AxxAxx/AxxSolder/photos/C210-029_cross_section.jpg

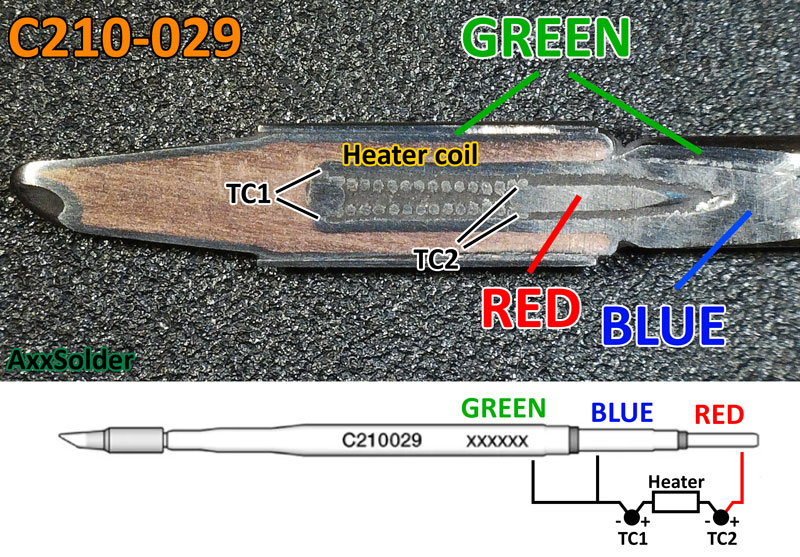
photos/C210-029_cross_section.jpg
