AxxAxx/AxxSolder/photos/C245-945_cross_section.jpg

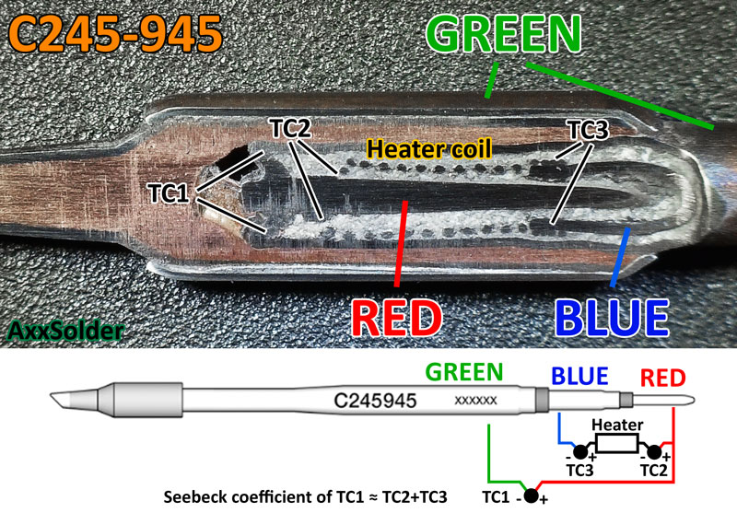
photos/C245-945_cross_section.jpg
