AxxAxx/AxxSolder/photos/cartridges_cross_sections.jpg

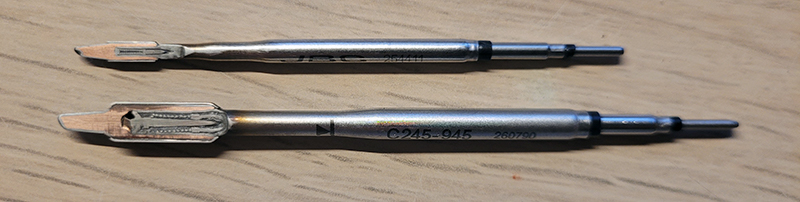
photos/cartridges_cross_sections.jpg
