AxxAxx/AxxSolder/photos/different_op-amps.png

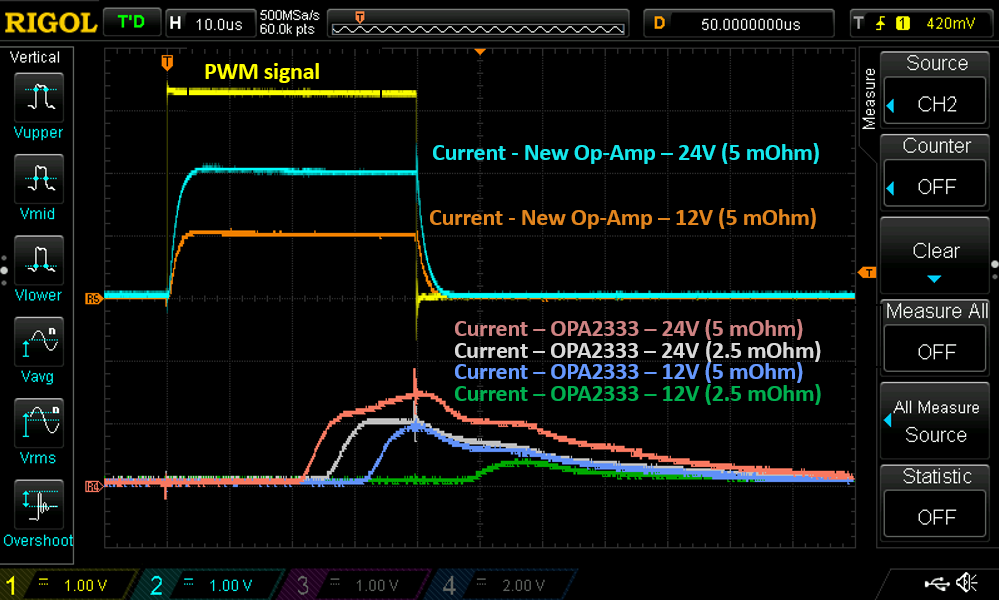
photos/different_op-amps.png
