AxxAxx/AxxSolder/photos/Internal_TCs.jpg

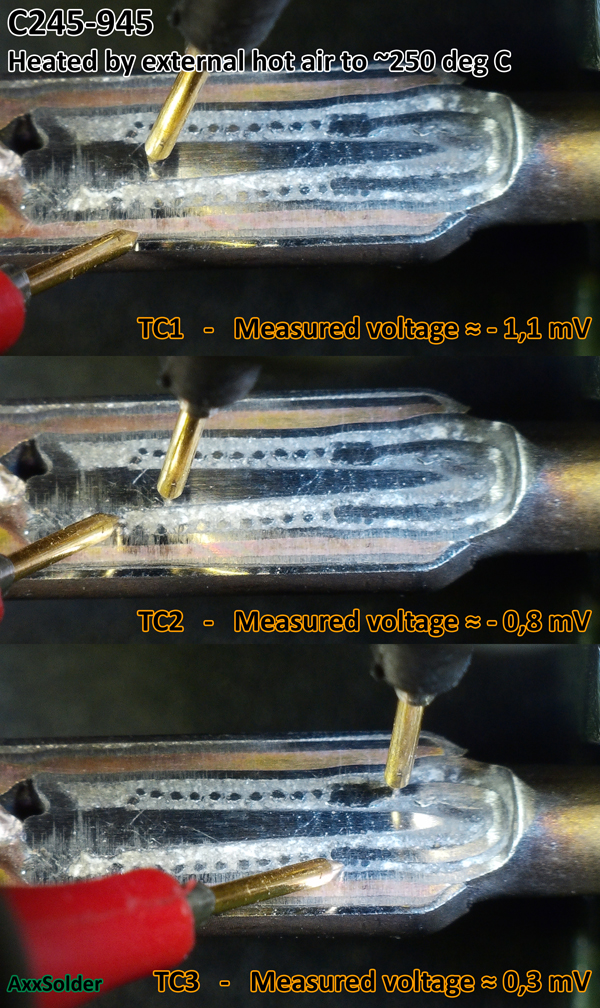
photos/Internal_TCs.jpg
