AxxAxx/AxxSolder/photos/JBC_DDE_temp_responce.jpg

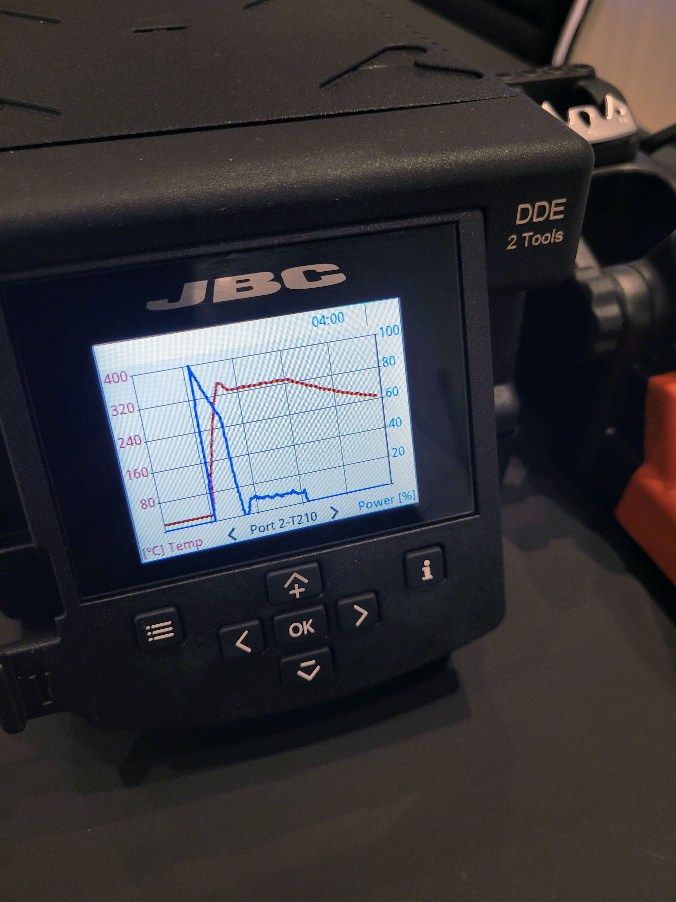
photos/JBC_DDE_temp_responce.jpg
