AxxAxx/AxxSolder/photos/MainScreen.jpg

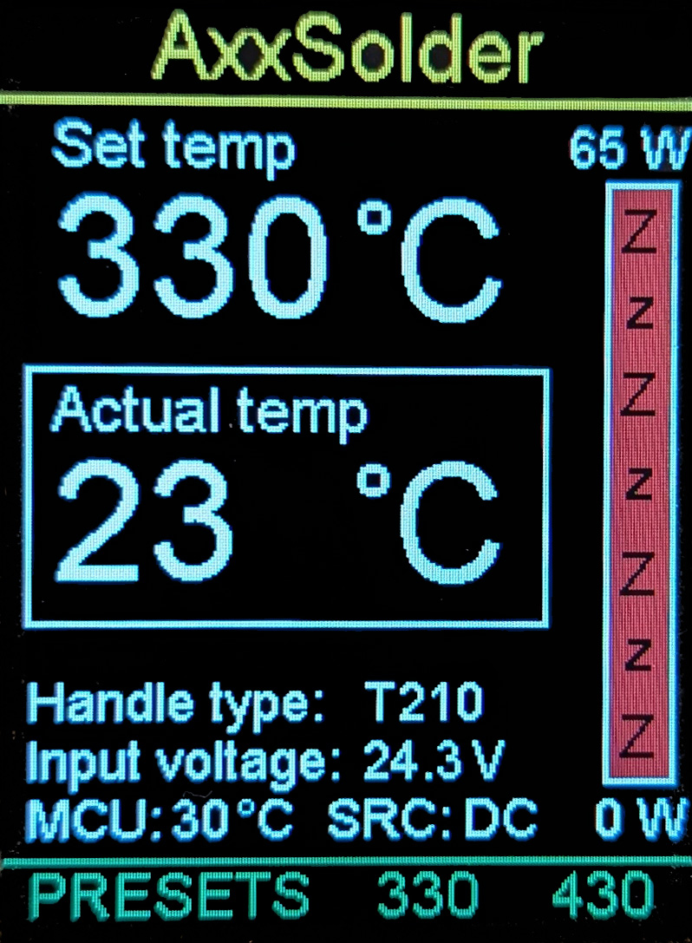
photos/MainScreen.jpg
