AxxAxx/AxxSolder/photos/PCB_image_x5.jpg

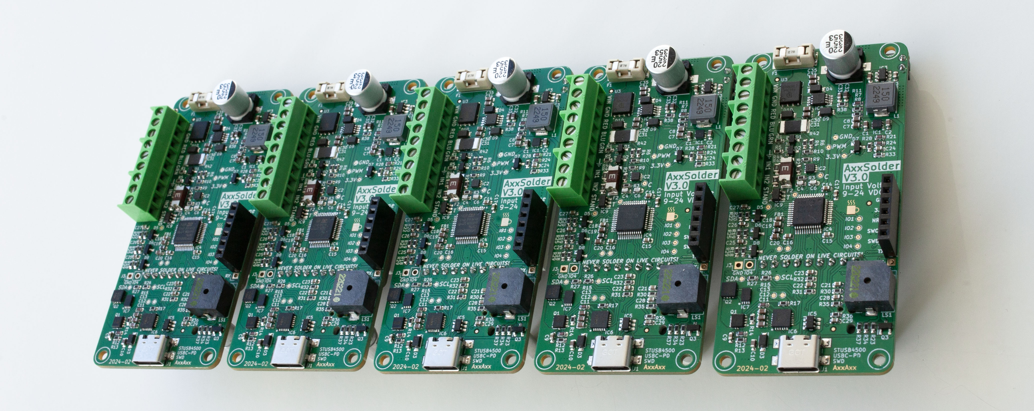
photos/PCB_image_x5.jpg
