AxxAxx/AxxSolder/photos/SELV_vs_PELV.PNG

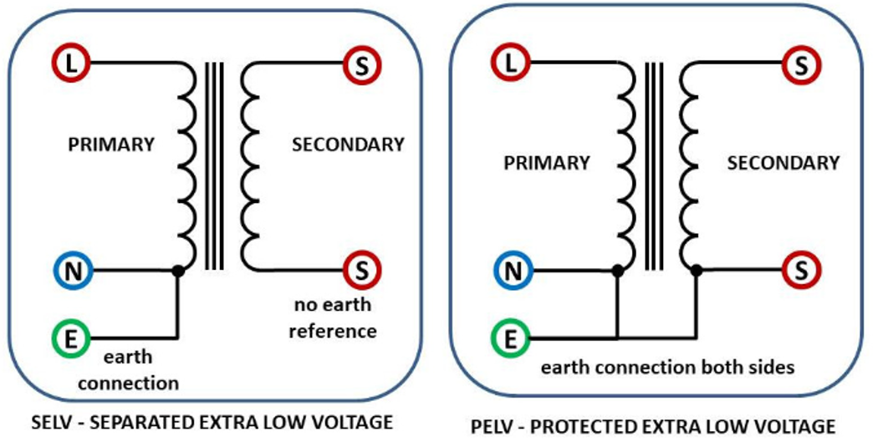
photos/SELV_vs_PELV.PNG
