AxxAxx/AxxSolder/photos/STprogrammer_2_15.png

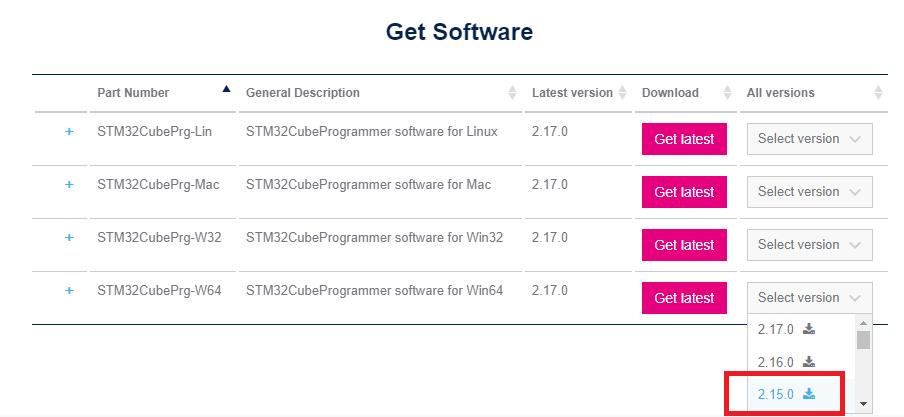
photos/STprogrammer_2_15.png
