AxxAxx/AxxSolder/CAD/Alternative_enclosures_and_designs/Geeboon Stand/Geeboon_Stand-0.3.3mf

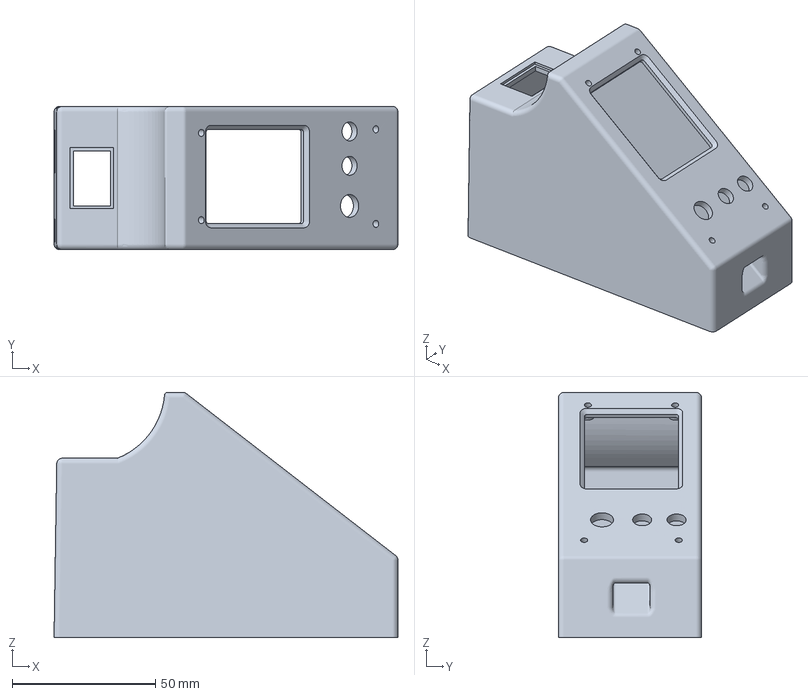
[picture p53: CAD file, 2025-07-13]
CAD/Alternative_enclosures_and_designs/Geeboon Stand/Geeboon_Stand-0.3.3mf
120.0 x 50.0 x 85.5 mm
