AxxAxx/AxxSolder/CAD/AxxSolder_JBC-ADS_stand/Encolsure_JBC-ADS.SLDPRT

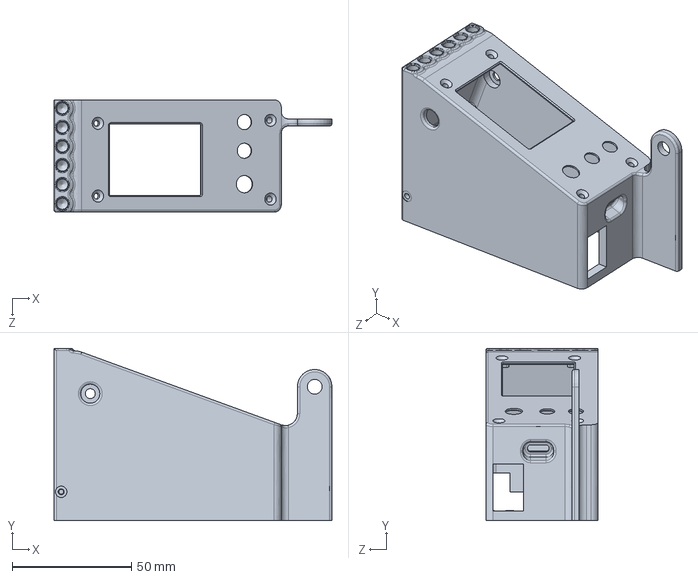
[picture p54: CAD file, 2024-11-03]
CAD/AxxSolder_JBC-ADS_stand/Encolsure_JBC-ADS.SLDPRT
116.5 x 72.2 x 47.1 mm
