AxxAxx/AxxSolder/CAD/AxxSolder_Portable/Encolsure_Portable.SLDPRT

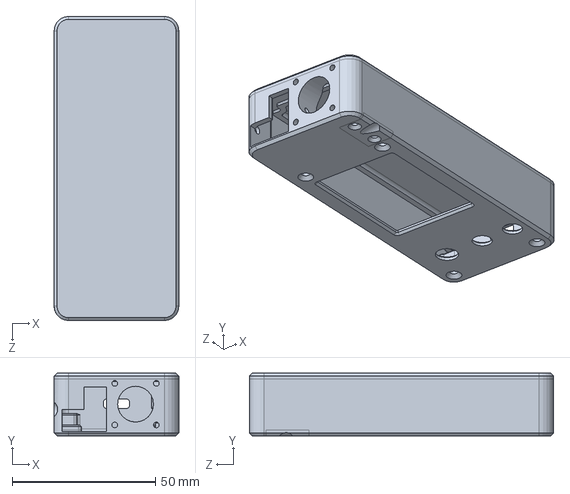
[picture p55: CAD file, 2024-11-18]
CAD/AxxSolder_Portable/Encolsure_Portable.SLDPRT
43.5 x 21.9 x 106.0 mm
