AxxAxx/AxxSolder/AxxSolder_hardware/3rd-parties-libraries/3D-models/PEC11J-9220F-S0015.stp

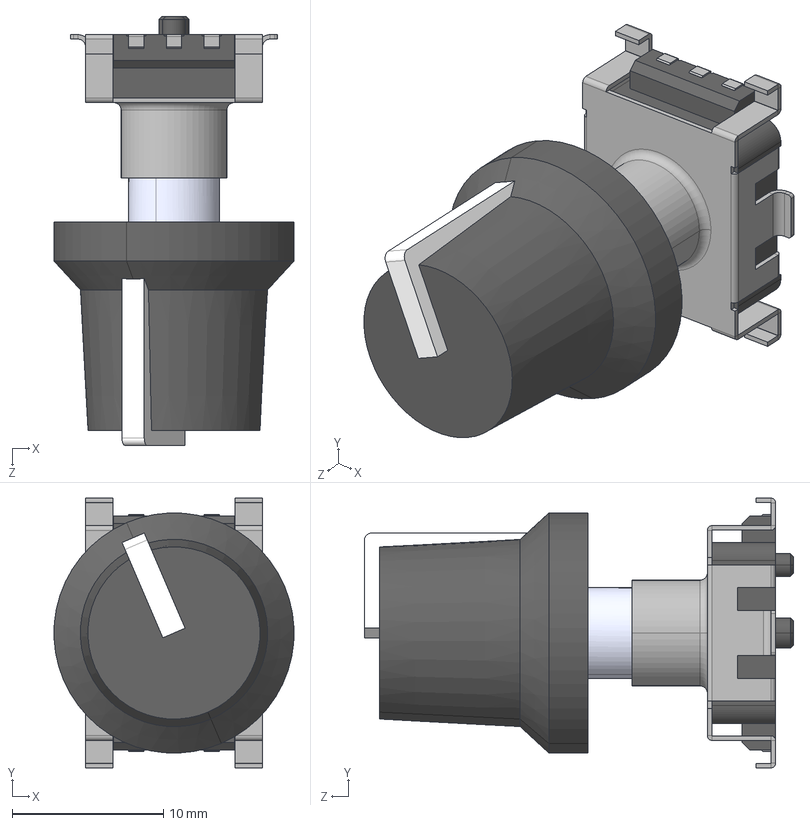
[picture p56: CAD file, 2024-03-02]
AxxSolder_hardware/3rd-parties-libraries/3D-models/PEC11J-9220F-S0015.stp
15.9 x 17.9 x 28.4 mm
Copy of Body.step.step^Copy of PEC11S.step.step_PEC11S.step
Copy of Shield.step.step^Copy of PEC11S.step.step_PEC11S.step
Copy of Pads.step.step^Copy of PEC11S.step.step_PEC11S.step
Copy of Part6.step^PEC11S.step
