AxxAxx/AxxSolder/CAD/Alternative_enclosures_and_designs/AixunT420_stand/enclosure.FCStd

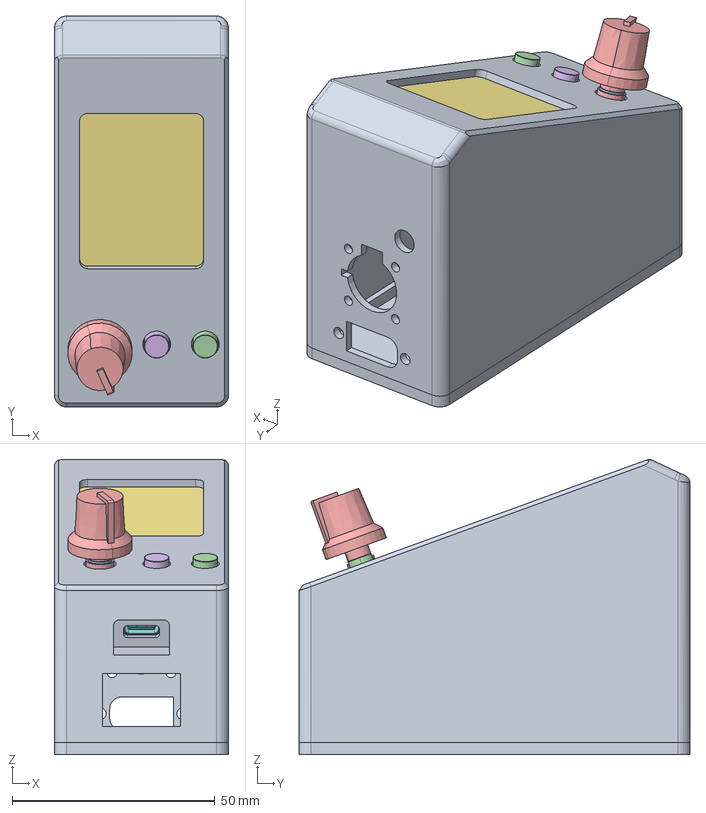
[picture p57: CAD file, 2025-07-18]
CAD/Alternative_enclosures_and_designs/AixunT420_stand/enclosure.FCStd
43.0 x 96.5 x 72.9 mm
Top
Board.step
10K.step
10K.step001
10K.step002
10K.step003
10K.step004
10K.step005
10K.step006
10K.step007
AP2112K-3.3.step
74HC4050D.step
MICROSD.step
BSS138.step
DISP_LCD_GENERIC_SPI_2.0IN_240X320.step
APX803-SAG.step
PinHeader_1x10_P2.54mm_Vertical.step
ADTSM6
ADTSM007
AxxSolder 1.4.1
ADTSM008
AxxSolder 1.6.1
Pins
AxxSolder 1.8.1
AxxSolder 1.8.002
AxxSolder 1.8.003
AxxSolder 1.8.4
SOT23 lower body
SOT23 Lead
SOT23 Lead001
SOT23 Lead002
SOT23 Upper body
PinsArrayLR
PinsArrayTB
SOD123W Lower body
SOD123W Lead
SOD123W Lead001
SOD123W Upper body
CMI-9653S-SMT-TR
PinKIdent
PinK
PinA
Pins001
BODY-SON
SOT23 lower body001
SOT23 Lead003
SOT23 Lead004
SOT23 Lead005
SOT23 Upper body001
PinsArrayL
FilletPinR
WSLP25125L000FEA
SOD123W Lower body001
SOD123W Lead002
SOD123W Lead003
SOD123W Upper body001
USB4110-GF-A
PinKIdent001
PinK001
PinA001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
