AxxAxx/AxxSolder/CAD/Alternative_enclosures_and_designs/AxxSolder-SDC02-Stand/STLs/tray.stl

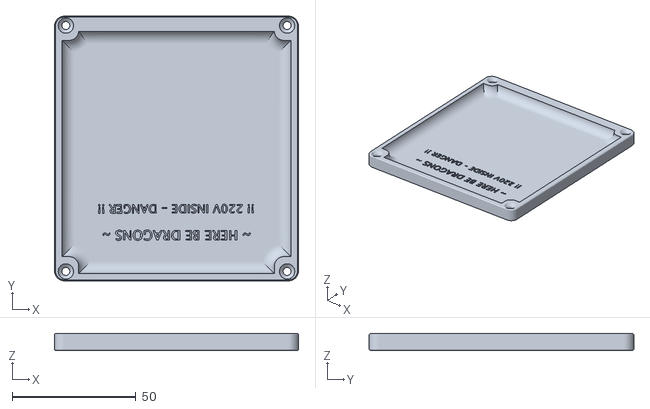
[picture p58: CAD file, 2026-09-08]
CAD/Alternative_enclosures_and_designs/AxxSolder-SDC02-Stand/STLs/tray.stl
98.7 x 107.1 x 7.00
