AxxAxx/AxxSolder/CAD/Alternative_enclosures_and_designs/Geeboon Stand/Mini Rocker.FCStd

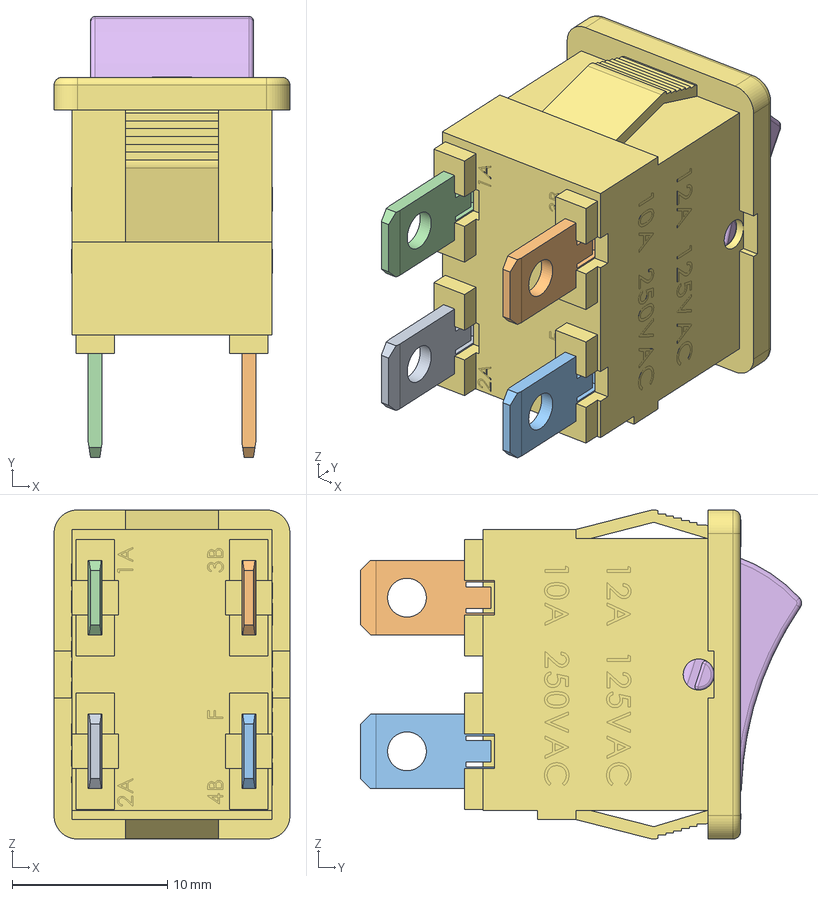
[picture p59: CAD file, 2025-07-13]
CAD/Alternative_enclosures_and_designs/Geeboon Stand/Mini Rocker.FCStd
15.2 x 28.4 x 21.2 mm
Switch Pin 1
Switch Pin 2
Switch Pin 3
Switch Pin 4
Weight Adjustment
Switch Rocker
Switch Surround
