AxxAxx/AxxSolder/CAD/AxxSolder_JBC-ADS_stand/Encolsure_JBC-AD-SF_SEPARATED_TOP_top.STEP

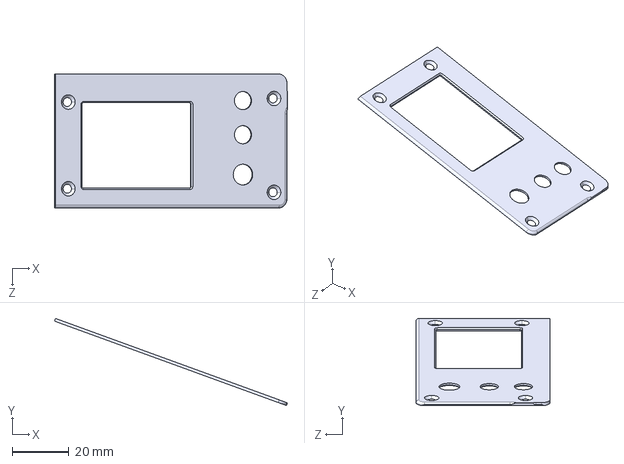
[picture p60: CAD file, 2024-11-03]
CAD/AxxSolder_JBC-ADS_stand/Encolsure_JBC-AD-SF_SEPARATED_TOP_top.STEP
81.9 x 30.6 x 47.1 mm
