AxxAxx/AxxSolder/CAD/AxxSolder_Portable/AxxSolder_Encolsure_Portable_Top_Earth_Stand_RockerSwitch.STEP

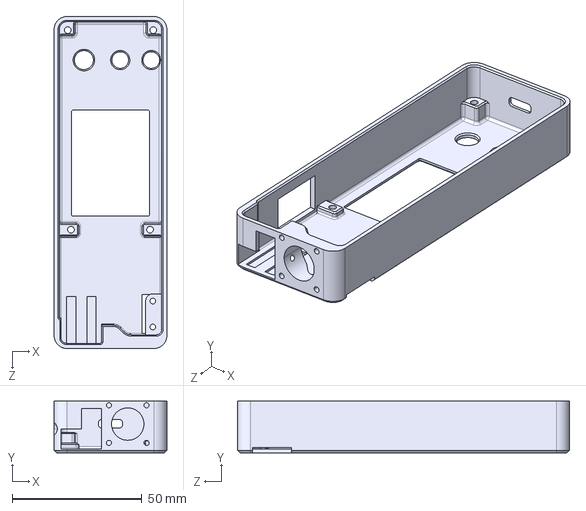
[picture p61: CAD file, 2024-11-18]
CAD/AxxSolder_Portable/AxxSolder_Encolsure_Portable_Top_Earth_Stand_RockerSwitch.STEP
43.5 x 20.0 x 128.0 mm
