AxxAxx/AxxSolder/AxxSolder_hardware/3rd-parties-libraries/3D-models/ADTSM6.STEP

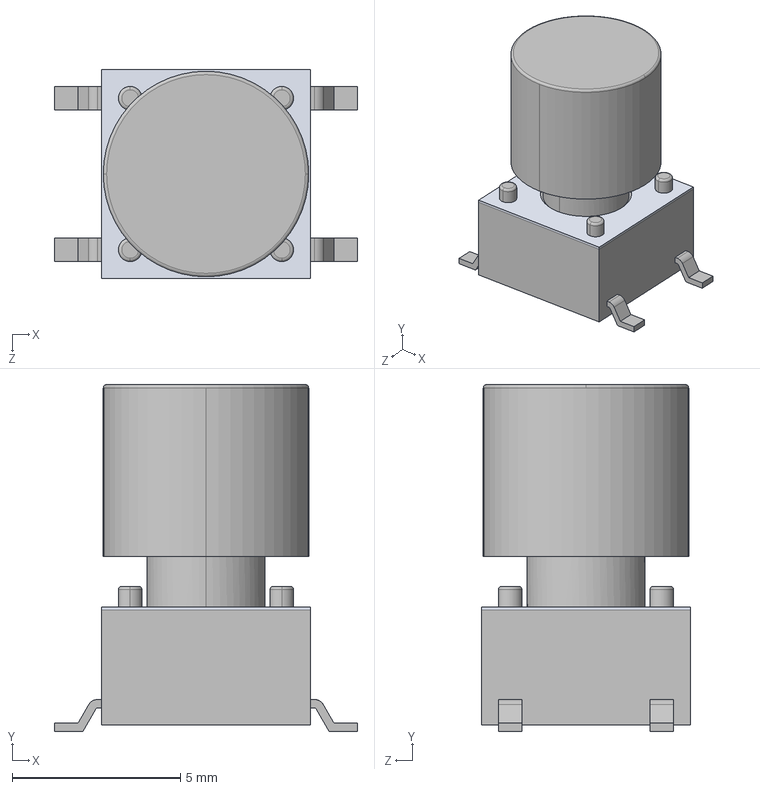
[picture p62: CAD file, 2024-03-02]
AxxSolder_hardware/3rd-parties-libraries/3D-models/ADTSM6.STEP
9.00 x 10.3 x 6.20 mm
