AxxAxx/AxxSolder/CAD/Alternative_enclosures_and_designs/Geeboon Stand/Geeboon_Stand.FCStd

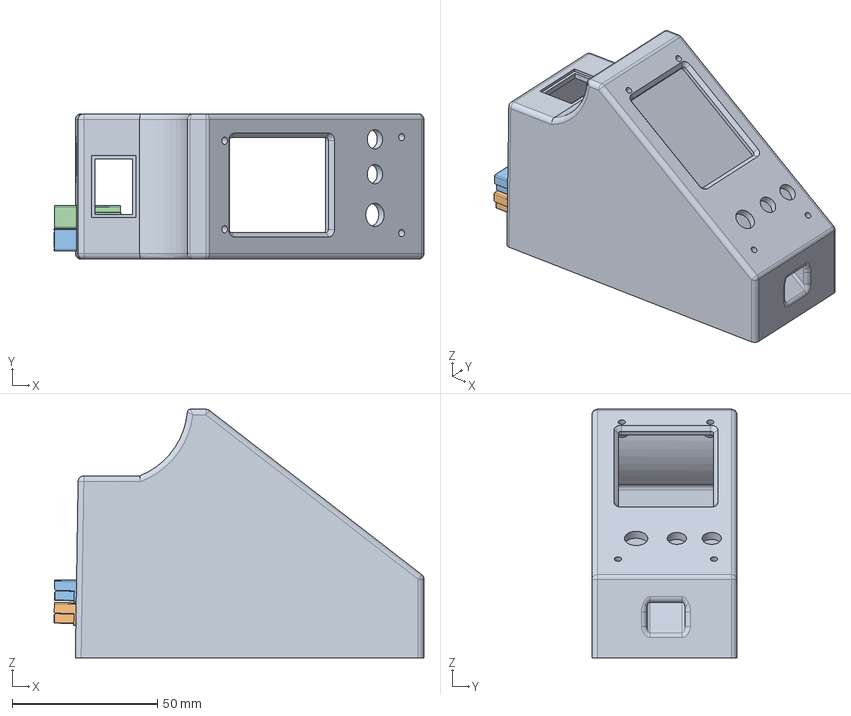
[picture p63: CAD file, 2025-07-13]
CAD/Alternative_enclosures_and_designs/Geeboon Stand/Geeboon_Stand.FCStd
127.3 x 50.0 x 85.5 mm
Enclosure Body
powerpole 15-45A Ground
powerpole 15-45A Negative
powerpole 15-45A Positive
