AxxAxx/AxxSolder/AxxSolder_hardware/3rd-parties-libraries/3D-models/WSLP25125L000FEA.stp

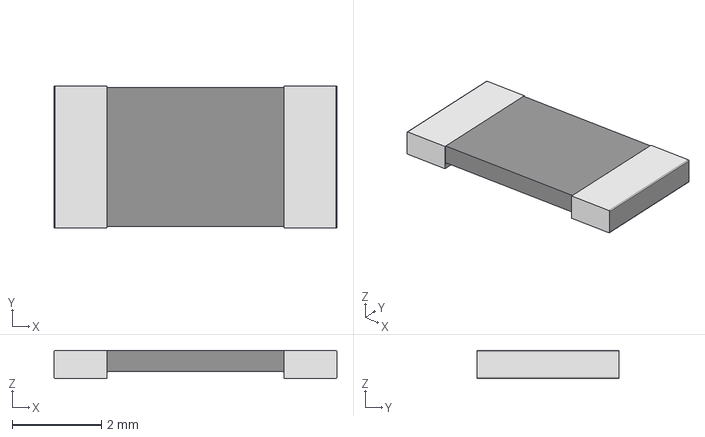
[picture p64: CAD file, 2024-03-02]
AxxSolder_hardware/3rd-parties-libraries/3D-models/WSLP25125L000FEA.stp
6.35 x 3.18 x 0.635 mm
