AxxAxx/AxxSolder/CAD/AxxSolder_Portable/AxxSolder_Encolsure_Portable_Bottom.STEP

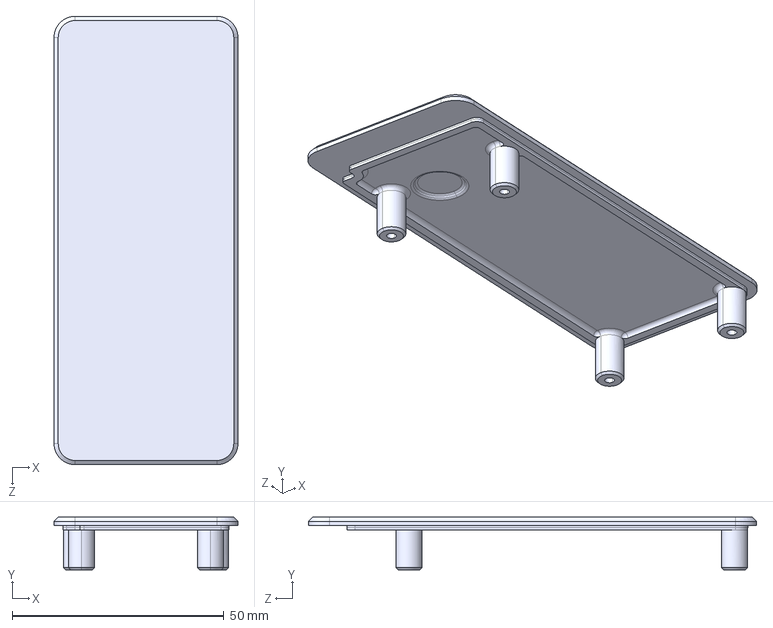
[picture p65: CAD file, 2024-09-20]
CAD/AxxSolder_Portable/AxxSolder_Encolsure_Portable_Bottom.STEP
43.5 x 12.5 x 106.0 mm
