AxxAxx/AxxSolder/AxxSolder_hardware/3rd-parties-libraries/3D-models/STM32G431CBU3.stp

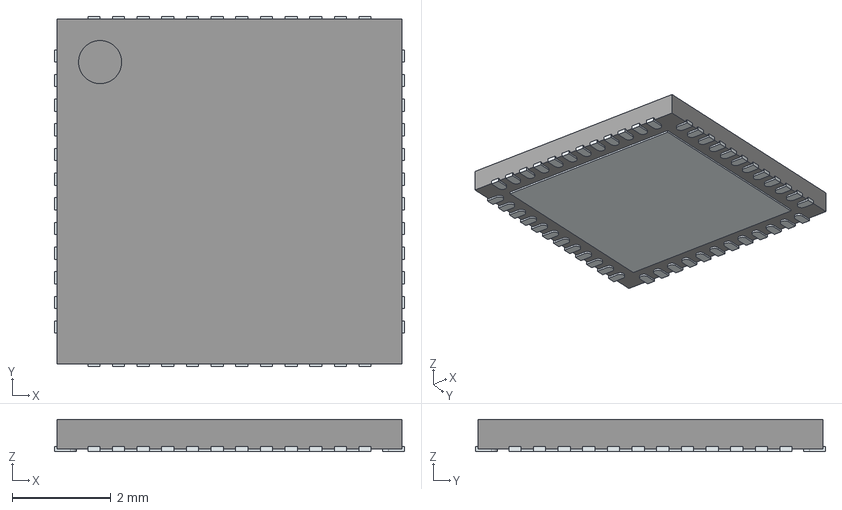
[picture p66: CAD file, 2024-03-02]
AxxSolder_hardware/3rd-parties-libraries/3D-models/STM32G431CBU3.stp
7.10 x 7.10 x 0.65 mm
ThermalPin
PinsArrayLR
PinsArrayTB
