AxxAxx/AxxSolder/CAD/Alternative_enclosures_and_designs/Geeboon Stand/AxxSolder-PCB.FCStd

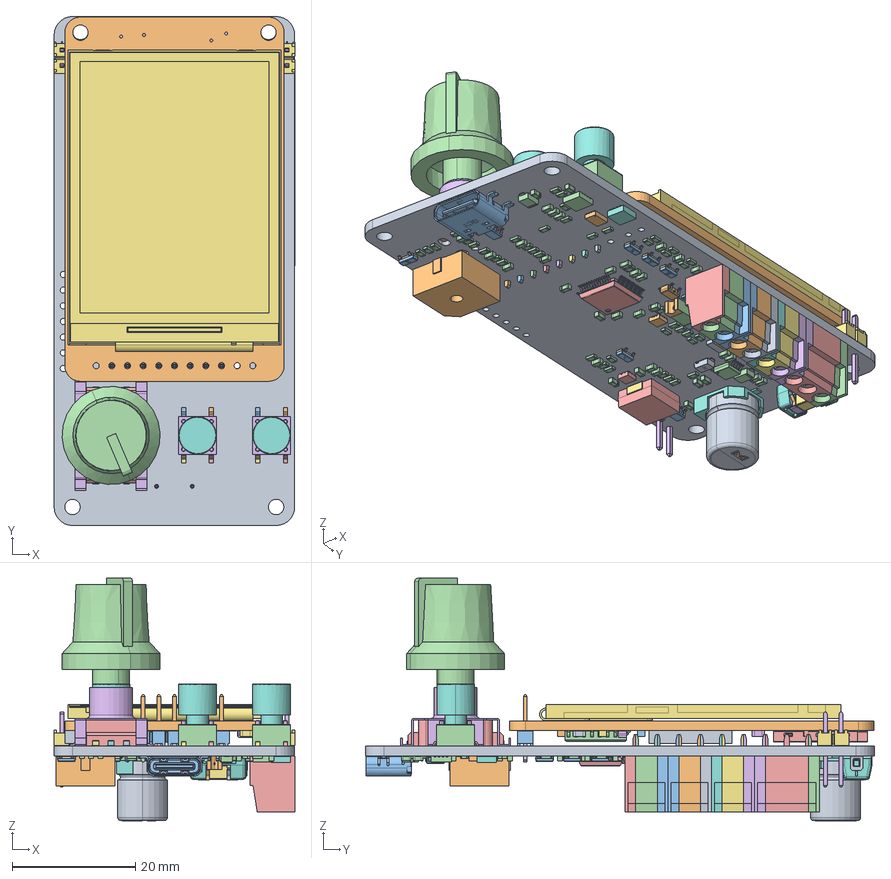
[picture p67: CAD file, 2025-07-13]
CAD/Alternative_enclosures_and_designs/Geeboon Stand/AxxSolder-PCB.FCStd
39.1 x 82.5 x 39.3 mm
Pcb_34f0
Board.step
10K.step
10K.step001
10K.step002
10K.step003
10K.step004
10K.step005
10K.step006
10K.step007
AP2112K-3.3.step
74HC4050D.step
MICROSD.step
BSS138.step
DISP_LCD_GENERIC_SPI_2.0IN_240X320.step
APX803-SAG.step
ADTSM6 x 3
ADTSM007 x 3
ADTSM008 x 3
ADTSM009 x 3
ADTSM010 x 3
ADTSM011 x 3
ADTSM012 x 3
ADTSM013 x 3
T-1S6-07-TSW-1-07-8-S
T-1S6-07-TSW-1-07-8-S001
T-1S6-07-TSW-1-07-8-S002
T-1S6-07-TSW-1-07-8-S003
T-1S6-07-TSW-1-07-8-S004
T-1S6-07-TSW-1-07-8-S005
T-1S6-07-TSW-1-07-8-S006
T-1S6-07-TSW-1-07-8-S007
T-1S6-07-TSW-1-07-8-S008
TSW-108-07-F-S_body
C23_C_0603_1608Metric_5e070203f8f2 x 35
Chamfer.stp
FilletPin1.stp
FilletPin2.stp
Pins
Pins001
Pins002
Pins003
Pins004
Pins005
Pins006
Pins007
Pins008
Pins009
CPA3.5_DX
CPA3.5_SX
CPA3.5_DX001
CPA3.5_SX001
CPA3.5_DX002
CPA3.5_SX002
CPA3.5_DX003
CPA3.5_SX003
SOT23 lower body x 5
SOT23 Lead x 5
SOT23 Lead001 x 5
SOT23 Lead002 x 5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
