AxxAxx/AxxSolder/CAD/AxxSolder_Portable/AxxSolder_Encolsure_Portable_Bottom_RockerSwitch.STEP

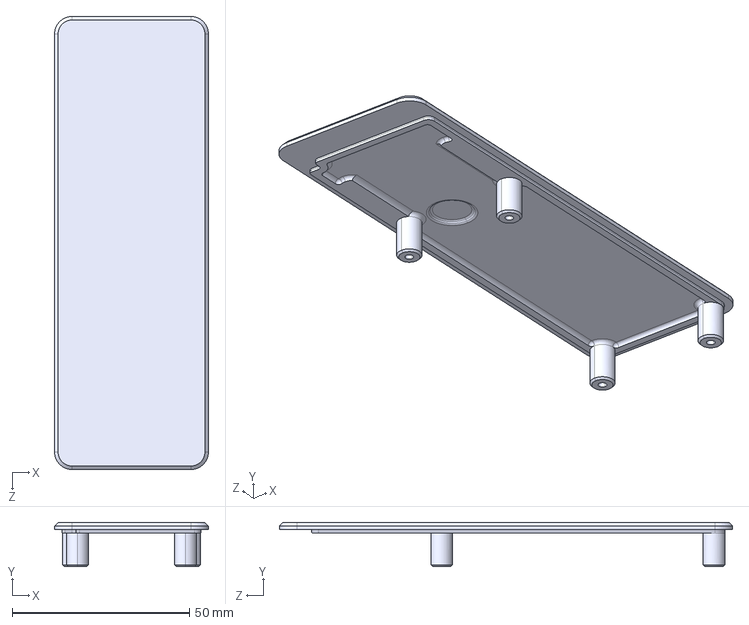
[picture p68: CAD file, 2024-09-20]
CAD/AxxSolder_Portable/AxxSolder_Encolsure_Portable_Bottom_RockerSwitch.STEP
43.5 x 12.5 x 128.0 mm
