AxxAxx/AxxSolder/AxxSolder_hardware/3rd-parties-libraries/3D-models/ESDA25W.stp

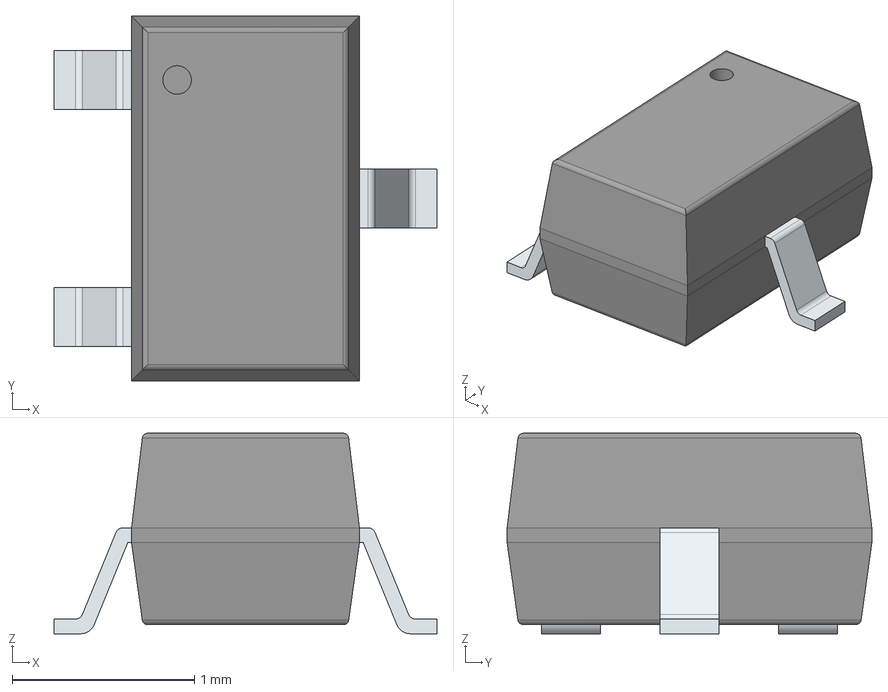
[picture p69: CAD file, 2024-03-02]
AxxSolder_hardware/3rd-parties-libraries/3D-models/ESDA25W.stp
2.10 x 2.00 x 1.10 mm
PinsArrayL
FilletPinR
