AxxAxx/AxxSolder/CAD/AxxSolder_JBC-ADS_stand/Mounting_Bracket_combined.STEP

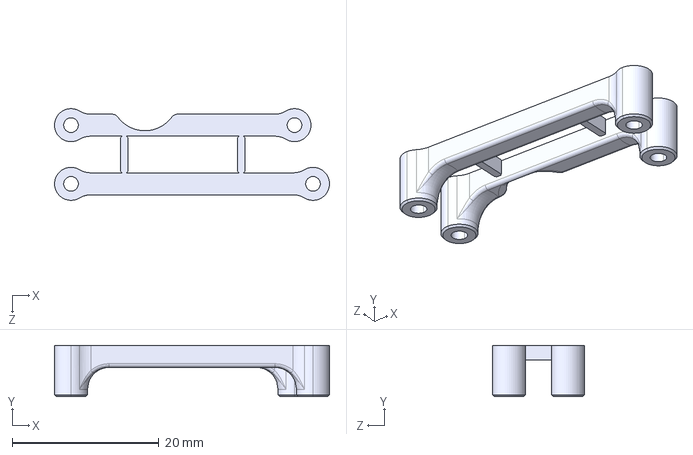
[picture p70: CAD file, 2024-05-20]
CAD/AxxSolder_JBC-ADS_stand/Mounting_Bracket_combined.STEP
37.5 x 7.00 x 12.5 mm
