AxxAxx/AxxSolder/AxxSolder_hardware/3rd-parties-libraries/3D-models/TLV1117-33IDCYR.stp

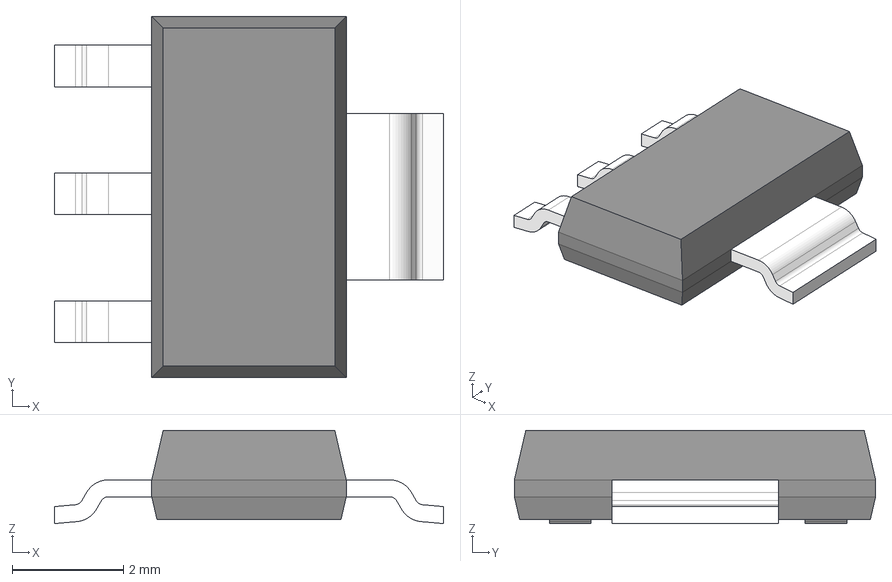
[picture p71: CAD file, 2024-03-02]
AxxSolder_hardware/3rd-parties-libraries/3D-models/TLV1117-33IDCYR.stp
7.00 x 6.50 x 1.68 mm
BODY-SOT
LEAD-SOT x 3
LEAD-SOT-WIDE
PIN1-ID
