AxxAxx/AxxSolder/CAD/AxxSolder_JBC-ADS_stand/Mounting_Bracket_B.STEP

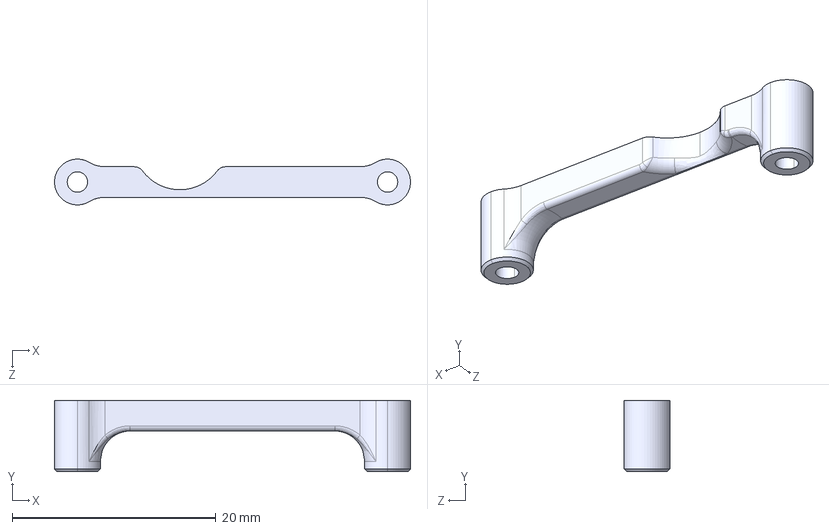
[picture p72: CAD file, 2024-03-02]
CAD/AxxSolder_JBC-ADS_stand/Mounting_Bracket_B.STEP
35.0 x 7.00 x 4.50 mm
