AxxAxx/AxxSolder/CAD/AxxSolder_Portable/powerpole 15-45A housing.step.SLDPRT

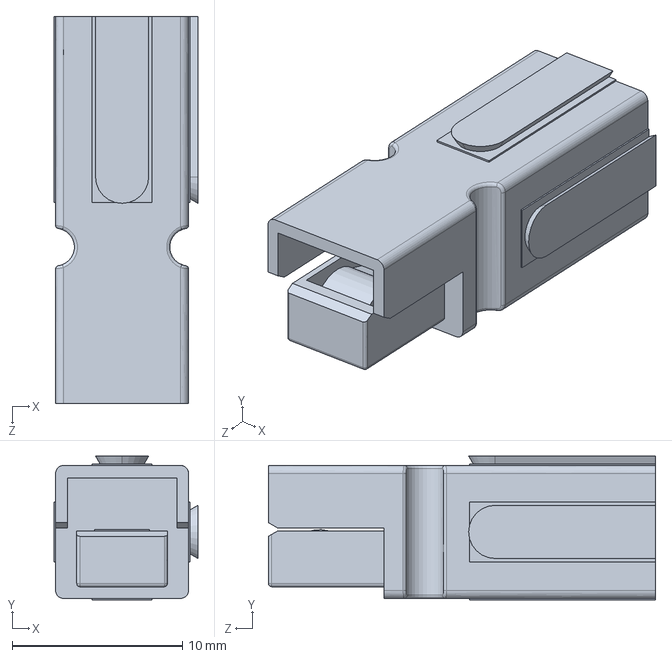
[picture p73: CAD file, 2024-03-02]
CAD/AxxSolder_Portable/powerpole 15-45A housing.step.SLDPRT
8.44 x 8.44 x 22.7 mm
