AxxAxx/AxxSolder/AxxSolder_hardware/3rd-parties-libraries/3D-models/TPD4E1B06DRLR.stp

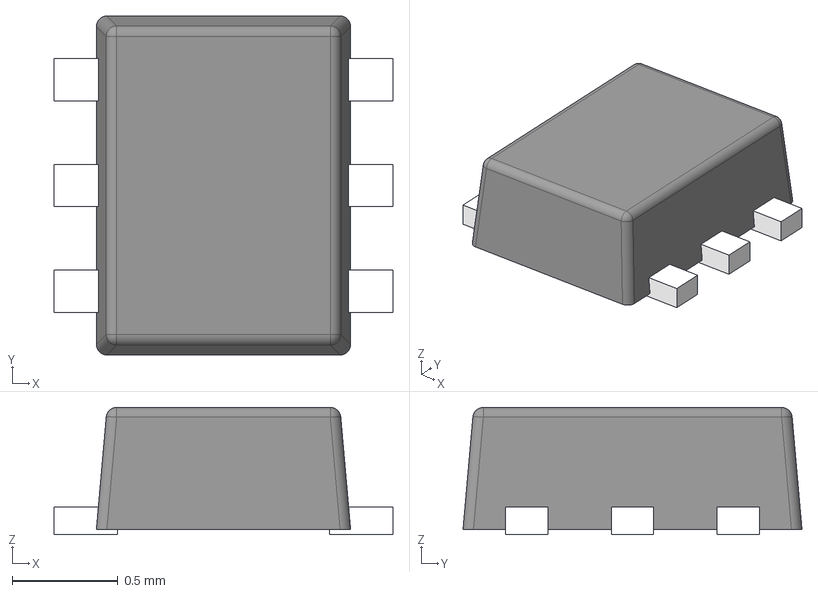
[picture p74: CAD file, 2024-03-02]
AxxSolder_hardware/3rd-parties-libraries/3D-models/TPD4E1B06DRLR.stp
1.60 x 1.60 x 0.6 mm
FRAME-DRL0006A
BODY-SOT
PIN1-ID
