AxxAxx/AxxSolder/CAD/AxxSolder_JBC-ADS_stand/Mounting_Bracket_A.STEP

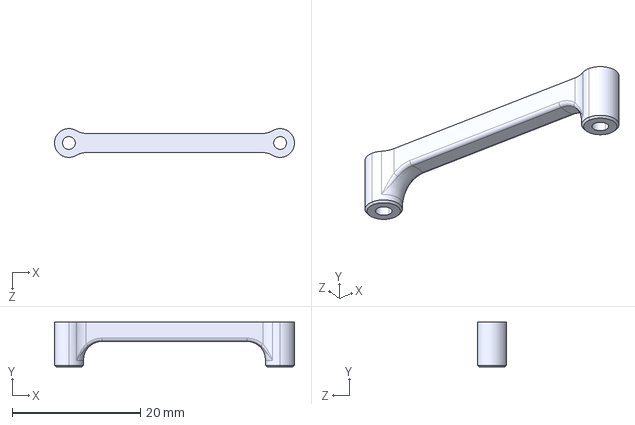
[picture p75: CAD file, 2024-03-02]
CAD/AxxSolder_JBC-ADS_stand/Mounting_Bracket_A.STEP
37.5 x 7.00 x 4.50 mm
