AxxAxx/AxxSolder/AxxSolder_hardware/3rd-parties-libraries/3D-models/STL10N3LLH5.stp

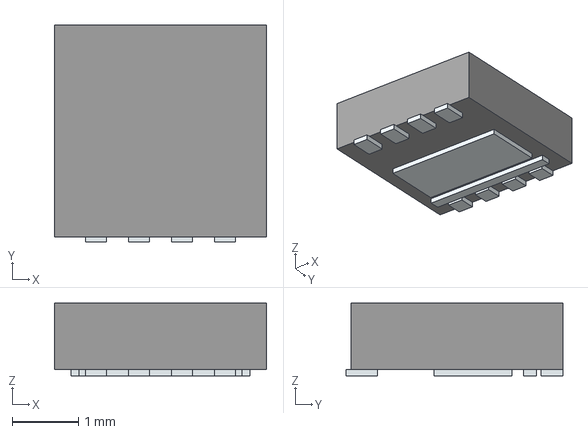
[picture p76: CAD file, 2024-03-02]
AxxSolder_hardware/3rd-parties-libraries/3D-models/STL10N3LLH5.stp
3.20 x 3.27 x 1.10 mm
Pins
