AxxAxx/AxxSolder/AxxSolder_hardware/3rd-parties-libraries/3D-models/TSW-102-07-T-S.stp

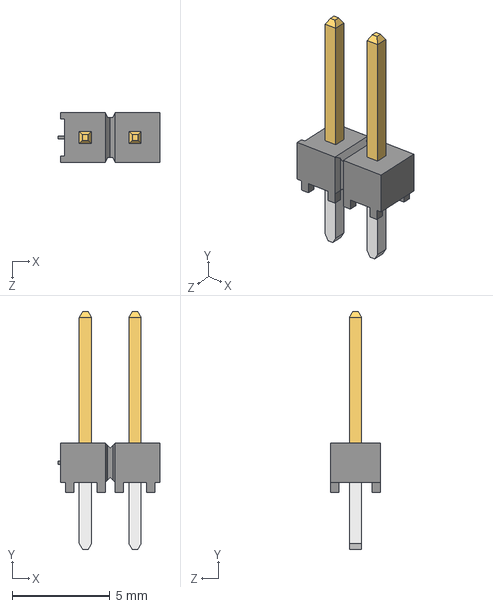
[picture p77: CAD file, 2024-03-02]
AxxSolder_hardware/3rd-parties-libraries/3D-models/TSW-102-07-T-S.stp
5.21 x 12.2 x 2.54 mm
T-1S6-17-TSW-1-24-2-S
TSW-102-24-L-S_body
