AxxAxx/AxxSolder/AxxSolder_hardware/3rd-parties-libraries/3D-models/STM32G431CBT6.stp

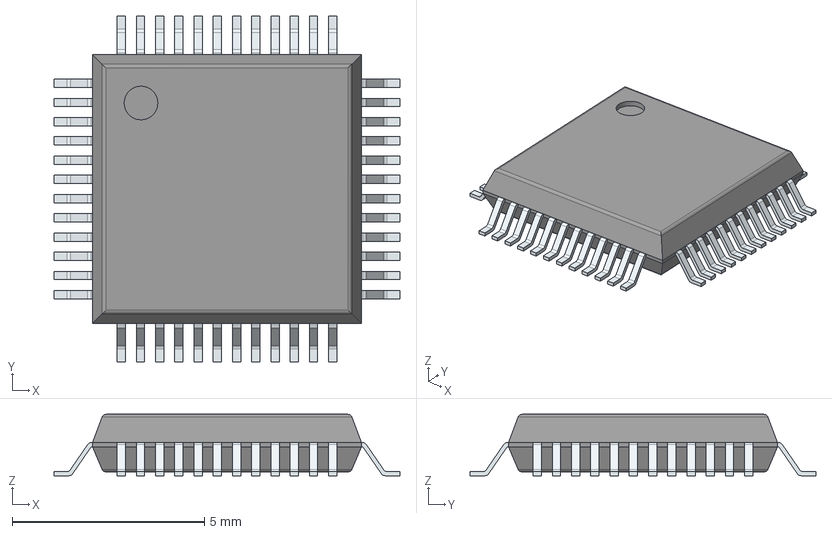
[picture p78: CAD file, 2024-03-02]
AxxSolder_hardware/3rd-parties-libraries/3D-models/STM32G431CBT6.stp
9.00 x 9.00 x 1.60 mm
PinsArrayLR
PinsArrayTB
