AxxAxx/AxxSolder/AxxSolder_hardware/3rd-parties-libraries/3D-models/USB4110-GF-A.stp

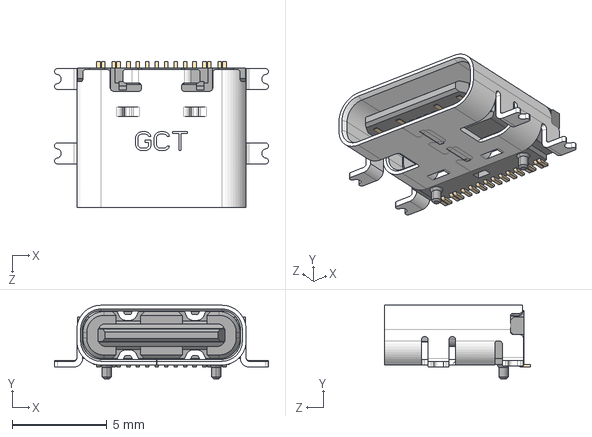
[picture p79: CAD file, 2024-03-02]
AxxSolder_hardware/3rd-parties-libraries/3D-models/USB4110-GF-A.stp
11.3 x 3.89 x 7.70 mm
