AxxAxx/AxxSolder/AxxSolder_hardware/3rd-parties-libraries/3D-models/OPA2387DSGT.stp

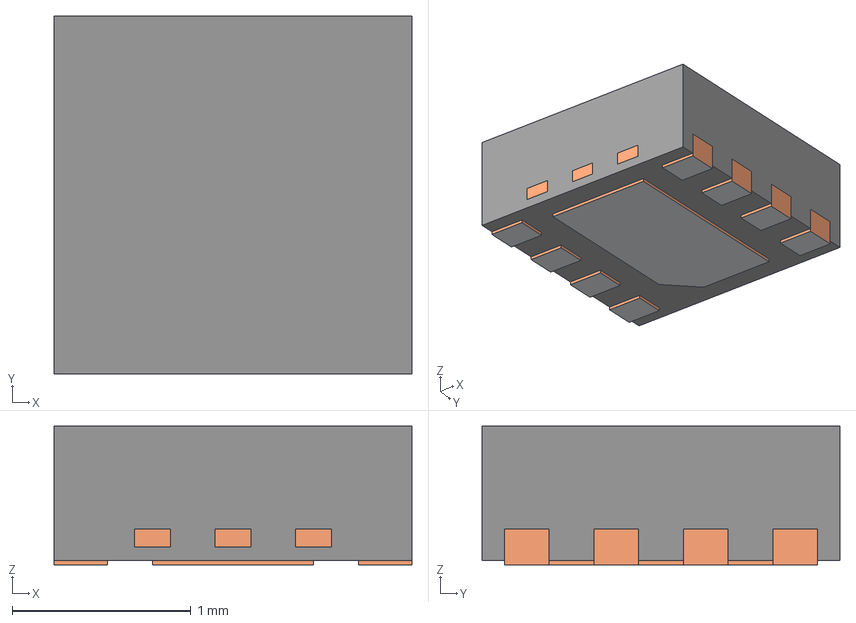
[picture p80: CAD file, 2024-03-02]
AxxSolder_hardware/3rd-parties-libraries/3D-models/OPA2387DSGT.stp
2.00 x 2.00 x 0.775 mm
BODY-SON
FRAME-DSG0008A
PIN1-ID
