AxxAxx/AxxSolder/AxxSolder_hardware/3rd-parties-libraries/3D-models/CMI-9653S-SMT-TR.step

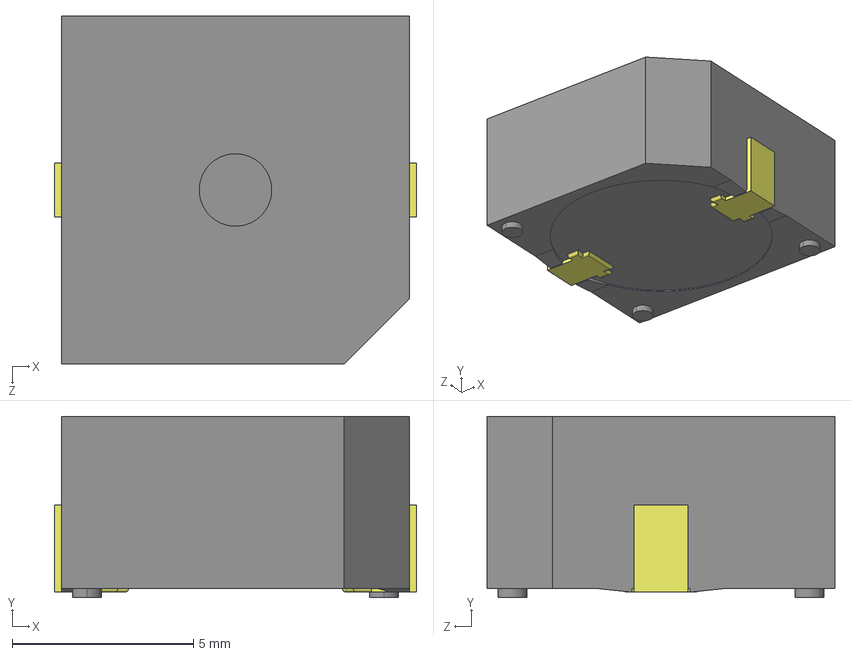
[picture p81: CAD file, 2024-03-02]
AxxSolder_hardware/3rd-parties-libraries/3D-models/CMI-9653S-SMT-TR.step
10.0 x 5.00 x 9.60 mm
