AxxAxx/AxxSolder/AxxSolder_hardware/3rd-parties-libraries/3D-models/NX2016SA-32M-EXS00A-CS06465.stp

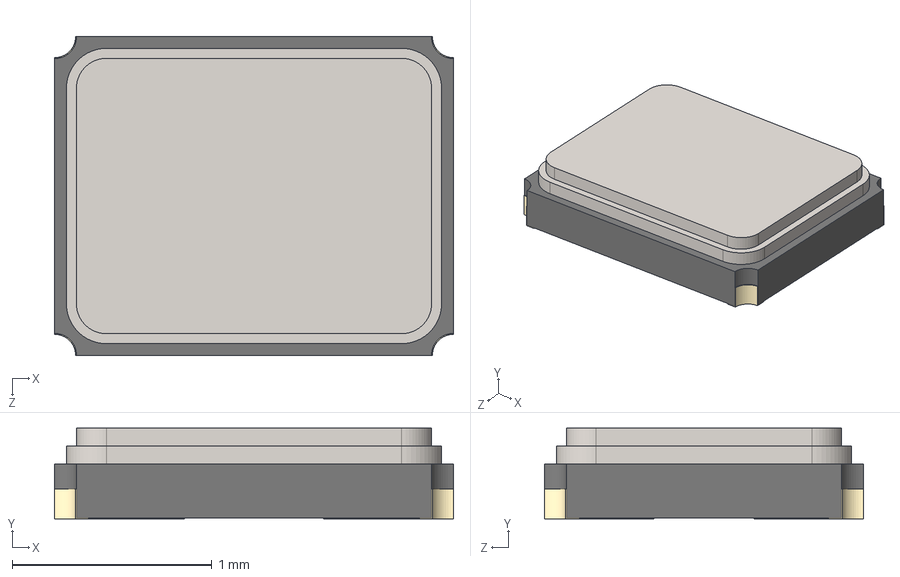
[picture p82: CAD file, 2024-03-02]
AxxSolder_hardware/3rd-parties-libraries/3D-models/NX2016SA-32M-EXS00A-CS06465.stp
2.00 x 0.455 x 1.60 mm
