AxxAxx/AxxSolder/AxxSolder_hardware/3rd-parties-libraries/3D-models/EMZR350ARA151MF80G.stp

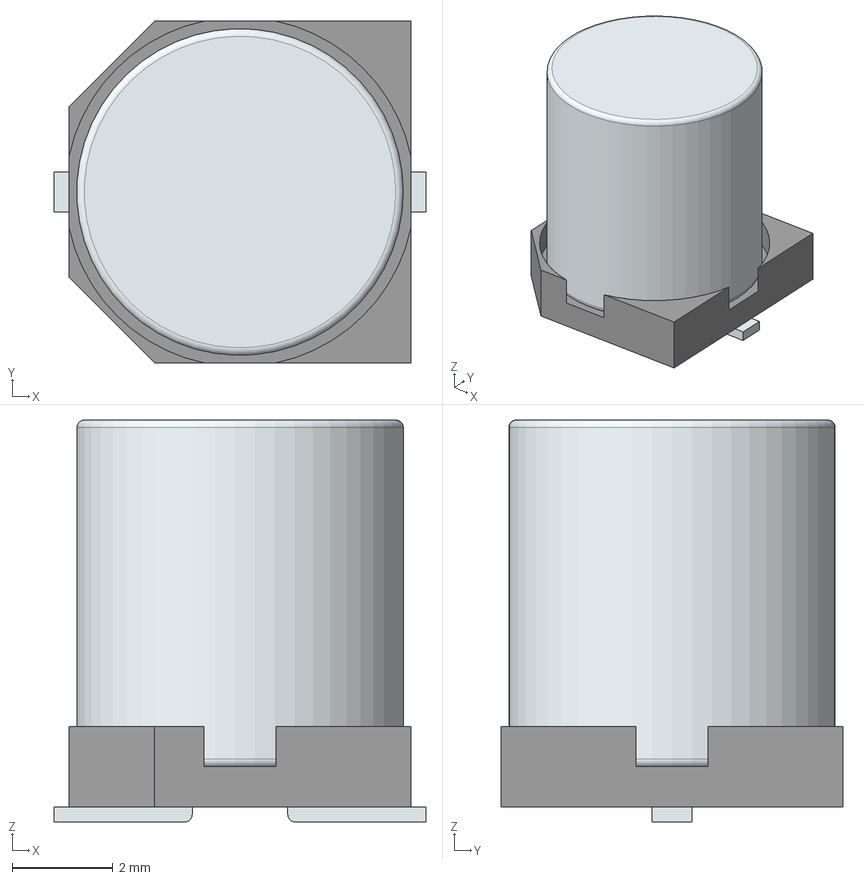
[picture p83: CAD file, 2024-03-02]
AxxSolder_hardware/3rd-parties-libraries/3D-models/EMZR350ARA151MF80G.stp
7.40 x 6.80 x 8.00 mm
Base
Pin1Fillet
Pin2Fillet
