AxxAxx/AxxSolder/AxxSolder_hardware/3rd-parties-libraries/3D-models/SMF4L24AT1G.stp

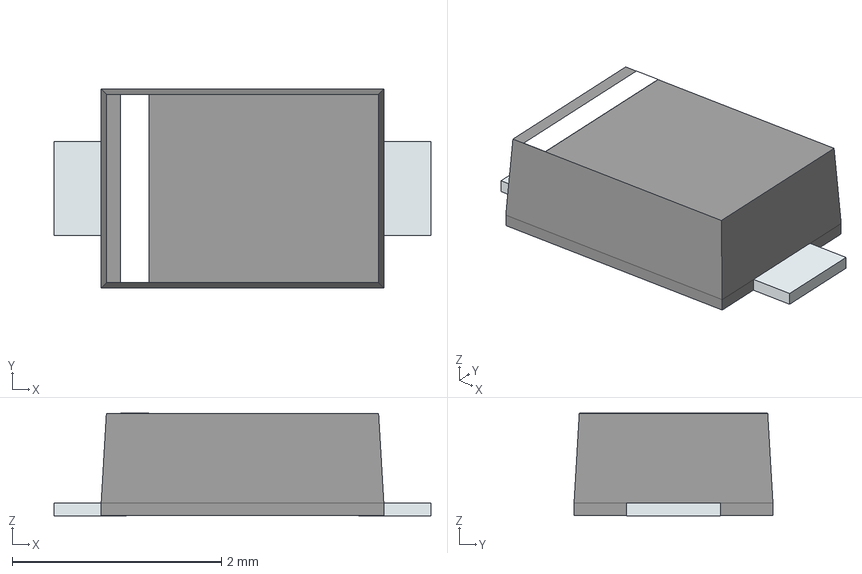
[picture p84: CAD file, 2024-03-02]
AxxSolder_hardware/3rd-parties-libraries/3D-models/SMF4L24AT1G.stp
3.60 x 1.90 x 0.98 mm
PinKIdent
PinK
PinA
