AxxAxx/AxxSolder/AxxSolder_hardware/3rd-parties-libraries/3D-models/TPD4E1U06DBVR.stp

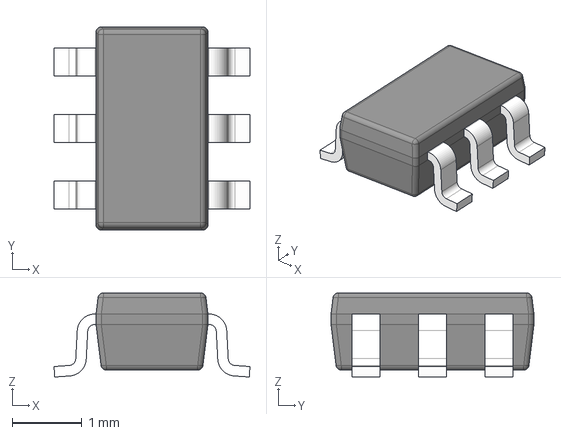
[picture p85: CAD file, 2024-03-02]
AxxSolder_hardware/3rd-parties-libraries/3D-models/TPD4E1U06DBVR.stp
2.80 x 2.90 x 1.20 mm
BODY-SOT
LEAD-SOT x 6
