AxxAxx/AxxSolder/AxxSolder_hardware/3rd-parties-libraries/3D-models/SMBJ24A.stp

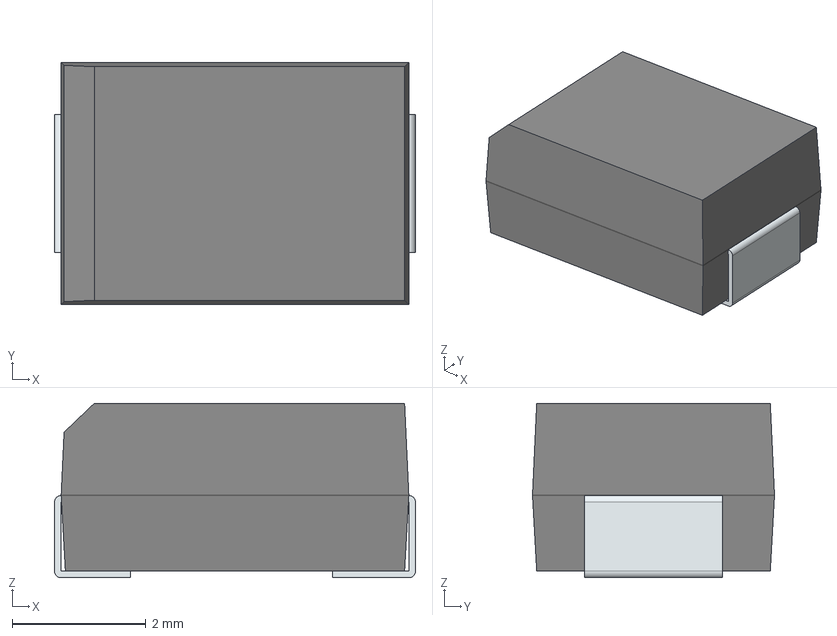
[picture p86: CAD file, 2024-03-02]
AxxSolder_hardware/3rd-parties-libraries/3D-models/SMBJ24A.stp
5.40 x 3.62 x 2.61 mm
FilletPin1
FilletPin2
