AxxAxx/AxxSolder/AxxSolder_hardware/3rd-parties-libraries/3D-models/EEV227M035A9MAA.stp

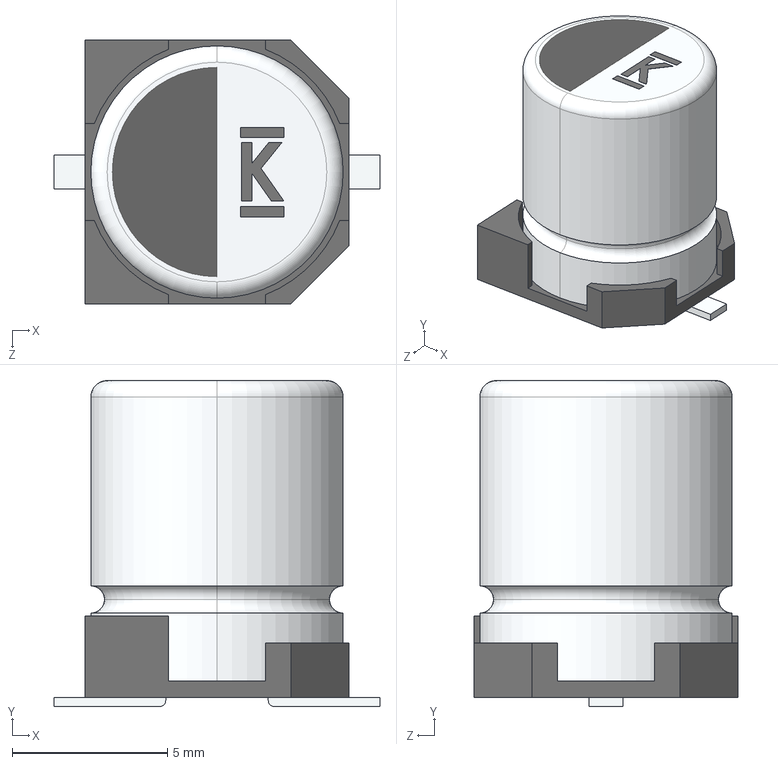
[picture p87: CAD file, 2024-03-02]
AxxSolder_hardware/3rd-parties-libraries/3D-models/EEV227M035A9MAA.stp
10.5 x 10.5 x 8.50 mm
