AxxAxx/AxxSolder/AxxSolder_hardware/3rd-parties-libraries/3D-models/STUSB4500QTR.stp

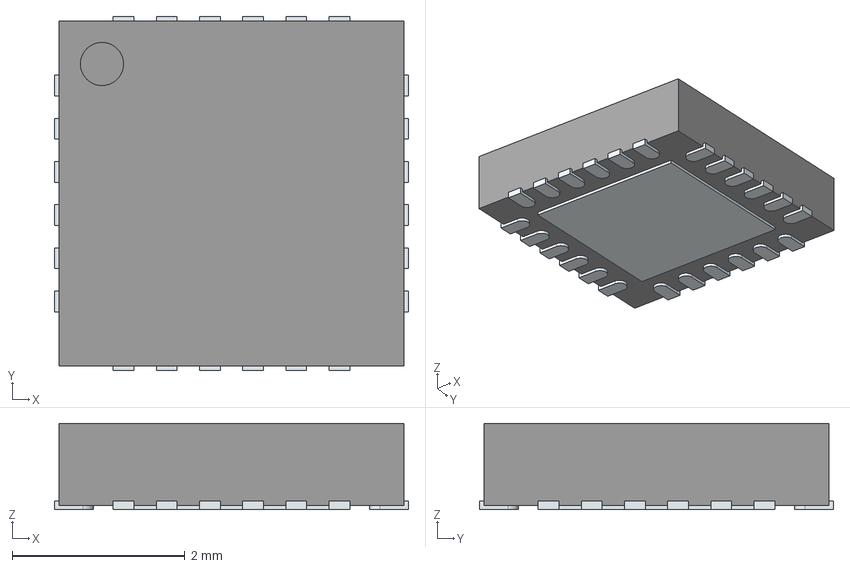
[picture p88: CAD file, 2024-03-02]
AxxSolder_hardware/3rd-parties-libraries/3D-models/STUSB4500QTR.stp
4.10 x 4.10 x 1.00 mm
ThermalPin
PinsArrayLR
PinsArrayTB
