AxxAxx/AxxSolder/AxxSolder_hardware/3rd-parties-libraries/3D-models/ESDA25P35-1U1M.stp

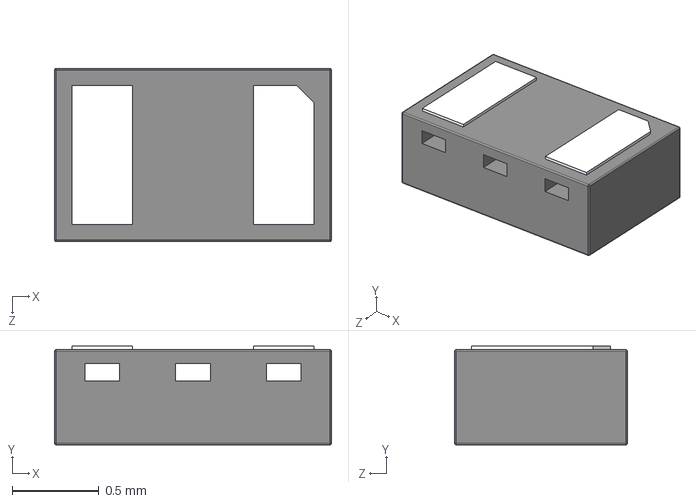
[picture p89: CAD file, 2024-03-02]
AxxSolder_hardware/3rd-parties-libraries/3D-models/ESDA25P35-1U1M.stp
1.60 x 0.57 x 1.00 mm
