AxxAxx/AxxSolder/AxxSolder_hardware/3rd-parties-libraries/3D-models/STL9P3LLH6.stp

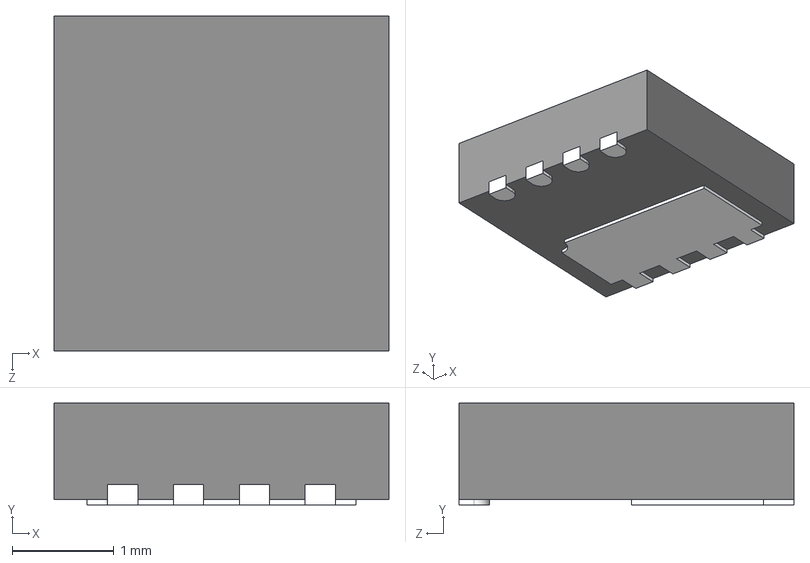
[picture p90: CAD file, 2024-03-02]
AxxSolder_hardware/3rd-parties-libraries/3D-models/STL9P3LLH6.stp
3.30 x 1 x 3.30 mm
