AxxAxx/AxxSolder/AxxSolder_hardware/3rd-parties-libraries/3D-models/BLM18HE601SN1D.stp

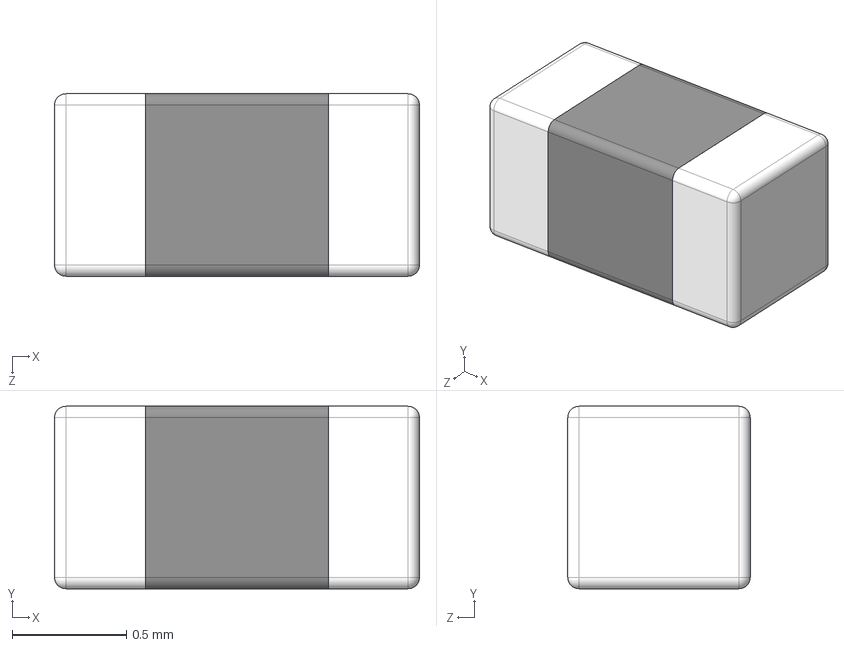
[picture p91: CAD file, 2024-03-02]
AxxSolder_hardware/3rd-parties-libraries/3D-models/BLM18HE601SN1D.stp
1.60 x 0.8 x 0.8 mm
