AxxAxx/AxxSolder/AxxSolder_hardware/3rd-parties-libraries/3D-models/SF-2410FP100W-2.stp

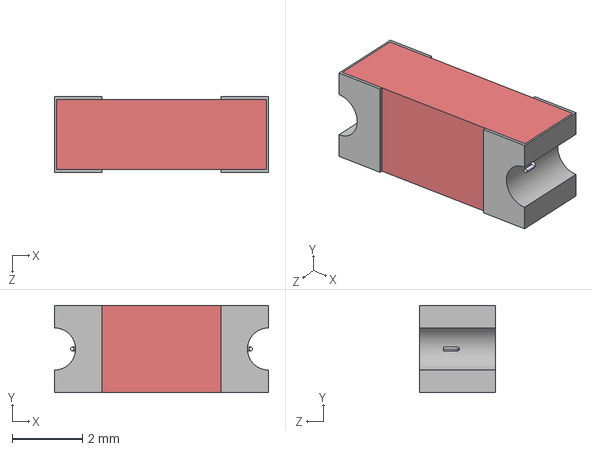
[picture p92: CAD file, 2024-03-02]
AxxSolder_hardware/3rd-parties-libraries/3D-models/SF-2410FP100W-2.stp
6.10 x 2.49 x 2.16 mm
