AxxAxx/AxxSolder/AxxSolder_hardware/3rd-parties-libraries/3D-models/SRP7028CC-150M.stp

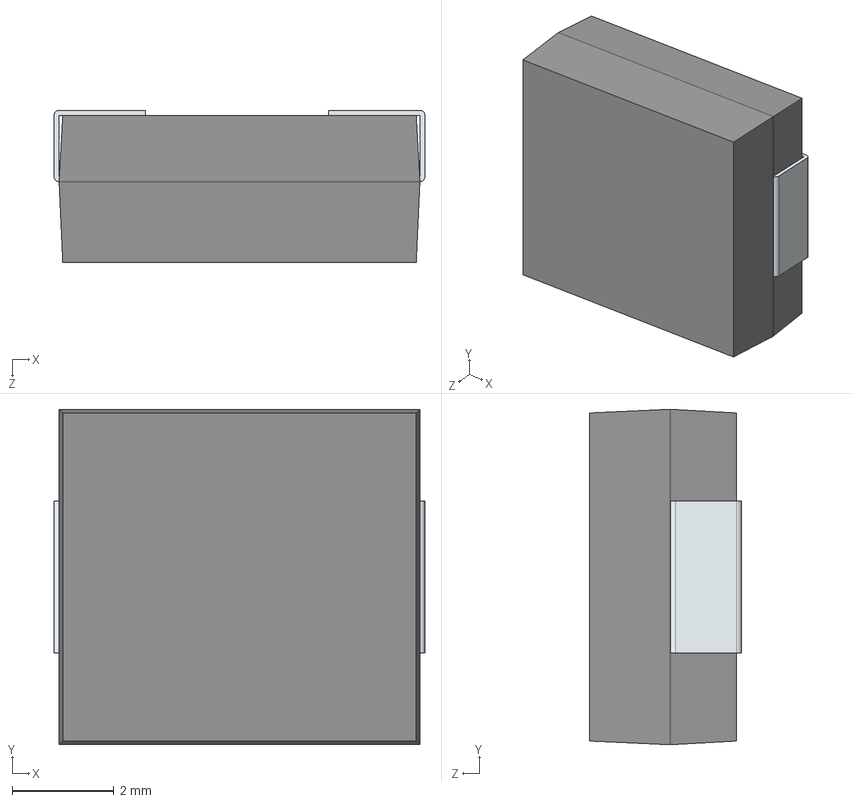
[picture p93: CAD file, 2023-10-06]
AxxSolder_hardware/3rd-parties-libraries/3D-models/SRP7028CC-150M.stp
7.30 x 6.60 x 3.00 mm
Chamfer.stp
FilletPin1.stp
FilletPin2.stp
