AxxAxx/AxxSolder/AxxSolder_hardware/3rd-parties-libraries/3D-models/LTC4440AHMS8E-5#PBF.stp

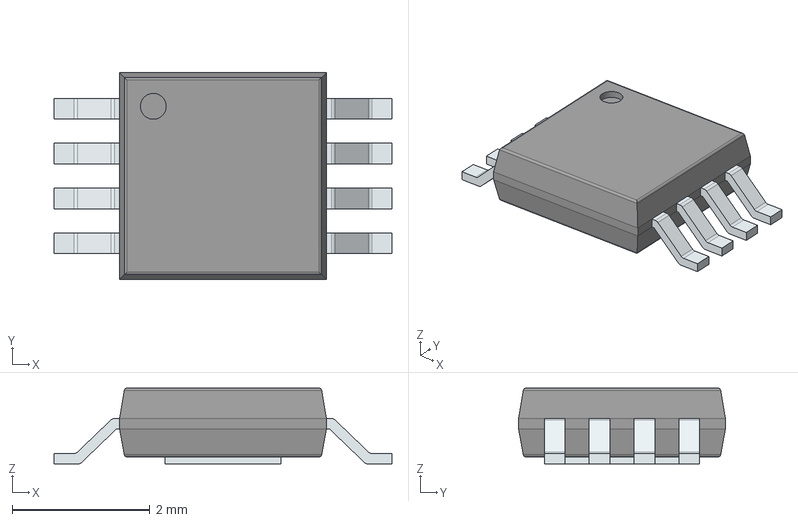
[picture p94: CAD file, 2023-09-02]
AxxSolder_hardware/3rd-parties-libraries/3D-models/LTC4440AHMS8E-5#PBF.stp
4.90 x 3.00 x 1.10 mm
PinsArrayLR
ThermalPad
