AxxAxx/AxxSolder/AxxSolder_hardware/3rd-parties-libraries/3D-models/EMZR500ARA331MJA0G.stp

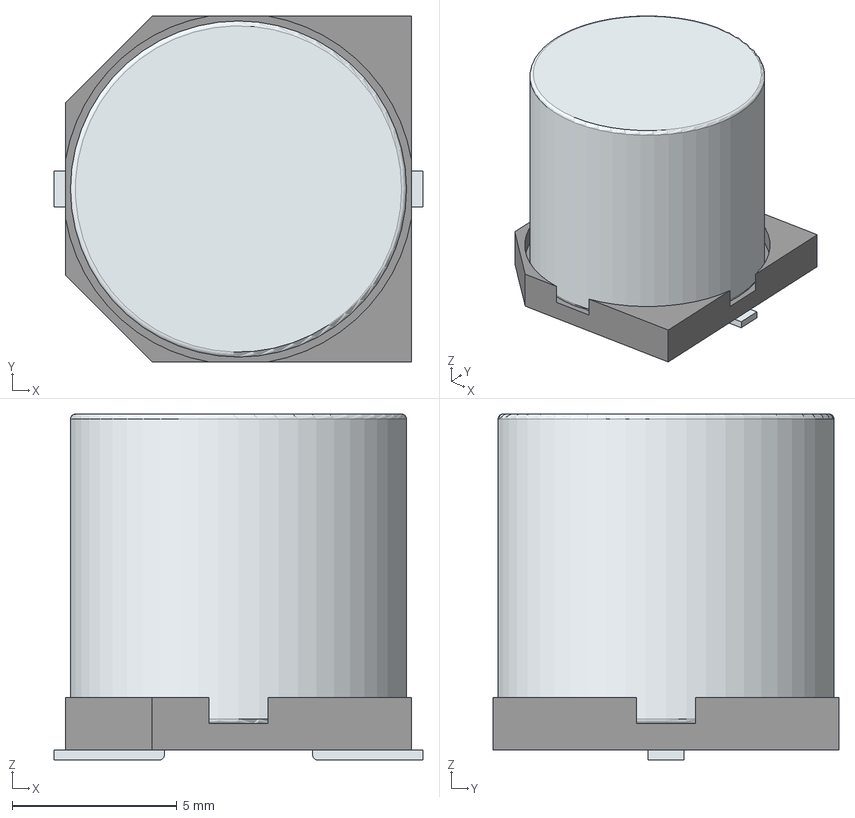
[picture p95: CAD file, 2023-09-02]
AxxSolder_hardware/3rd-parties-libraries/3D-models/EMZR500ARA331MJA0G.stp
11.2 x 10.5 x 10.5 mm
Base
Pin1Fillet
Pin2Fillet
