AxxAxx/AxxSolder/AxxSolder_hardware/3rd-parties-libraries/3D-models/INA281A5QDBVRQ1.stp

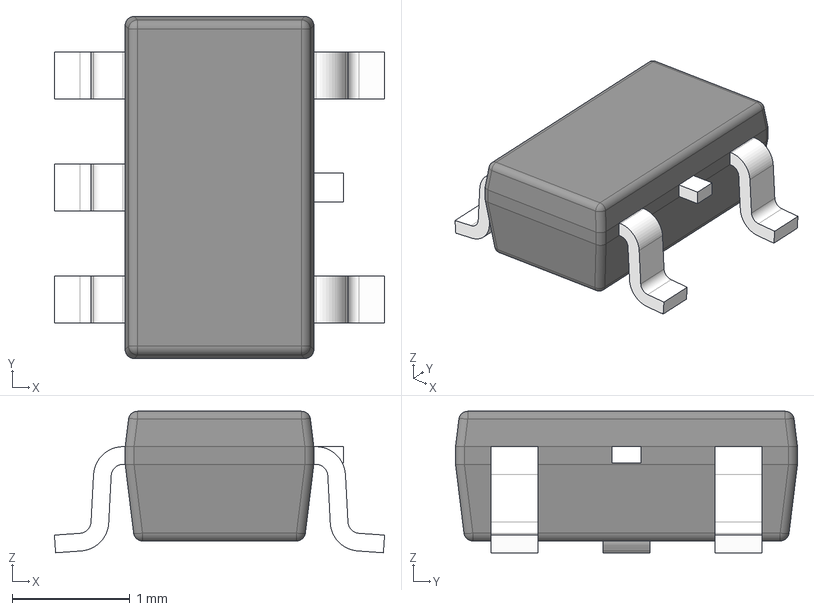
[picture p96: CAD file, 2023-09-02]
AxxSolder_hardware/3rd-parties-libraries/3D-models/INA281A5QDBVRQ1.stp
2.80 x 2.90 x 1.20 mm
BODY-SOT
LEAD-SOT x 5
LEAD-DUMMY
