AxxAxx/AxxSolder/AxxSolder_hardware/3rd-parties-libraries/3D-models/LD1117AS33TR.stp

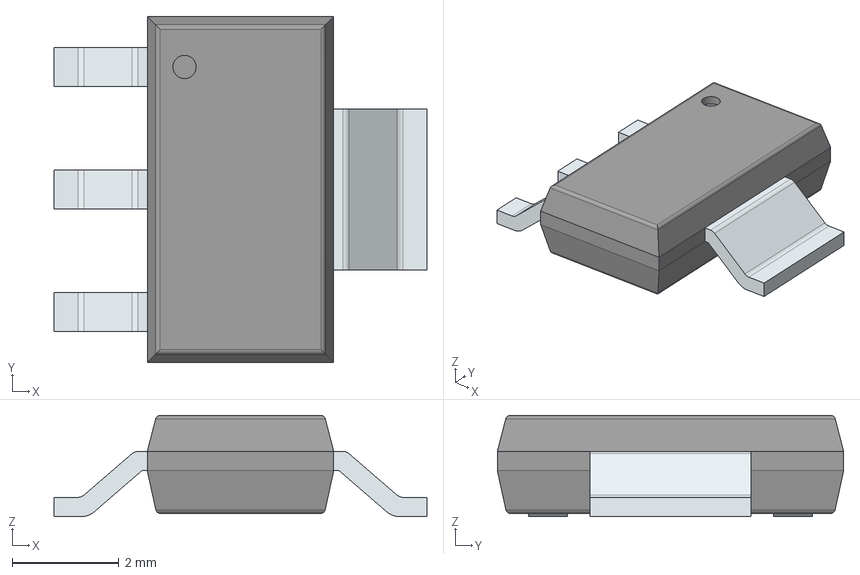
[picture p97: CAD file, 2023-09-02]
AxxSolder_hardware/3rd-parties-libraries/3D-models/LD1117AS33TR.stp
7.00 x 6.50 x 1.90 mm
PinsArrayL
FilletPinR
