AxxAxx/AxxSolder/AxxSolder_hardware/3rd-parties-libraries/3D-models/BSC014N04LS.stp

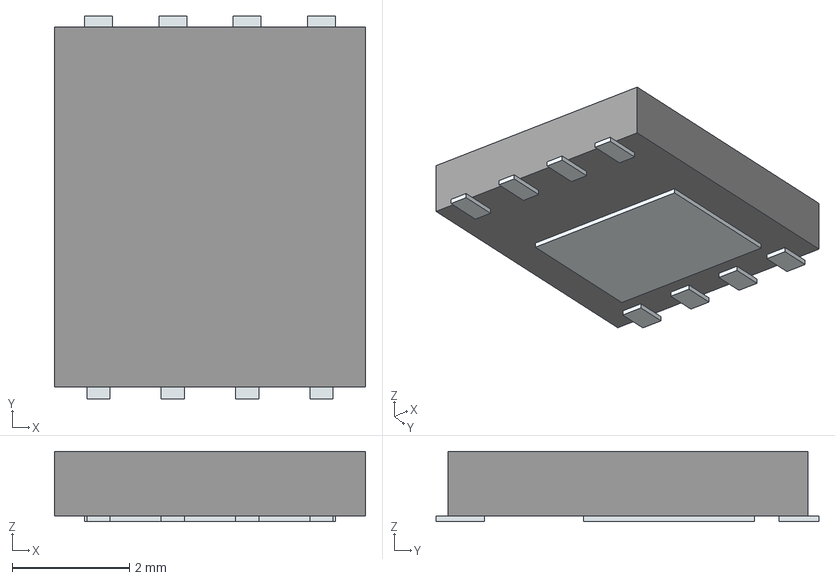
[picture p98: CAD file, 2023-09-02]
AxxSolder_hardware/3rd-parties-libraries/3D-models/BSC014N04LS.stp
5.32 x 6.54 x 1.20 mm
Pins
