AxxAxx/AxxSolder/AxxSolder_hardware/3rd-parties-libraries/3D-models/BAT54S,215.stp

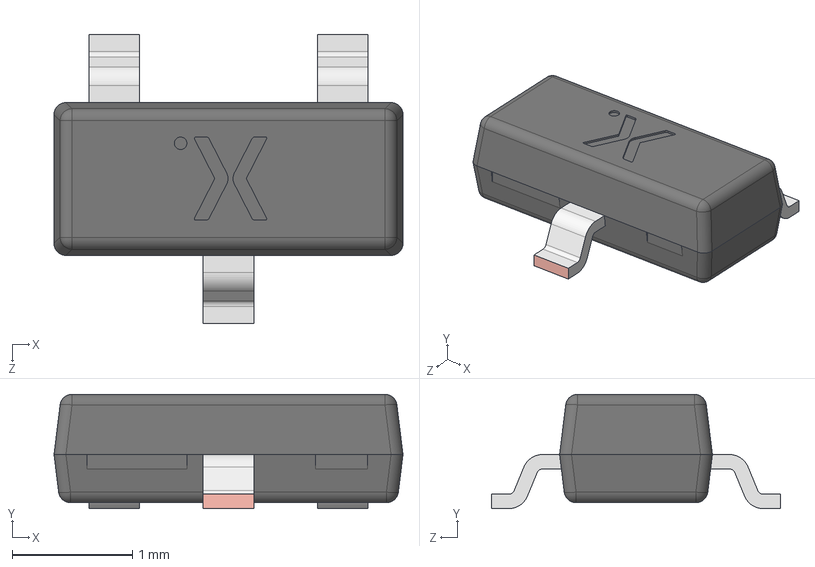
[picture p99: CAD file, 2023-09-02]
AxxSolder_hardware/3rd-parties-libraries/3D-models/BAT54S,215.stp
2.90 x 0.95 x 2.40 mm
SOT23 lower body
SOT23 Lead x 3
SOT23 Upper body
