AxxAxx/AxxSolder/AxxSolder_hardware/3rd-parties-libraries/3D-models/TPD2E2U06QDBZRQ1.stp

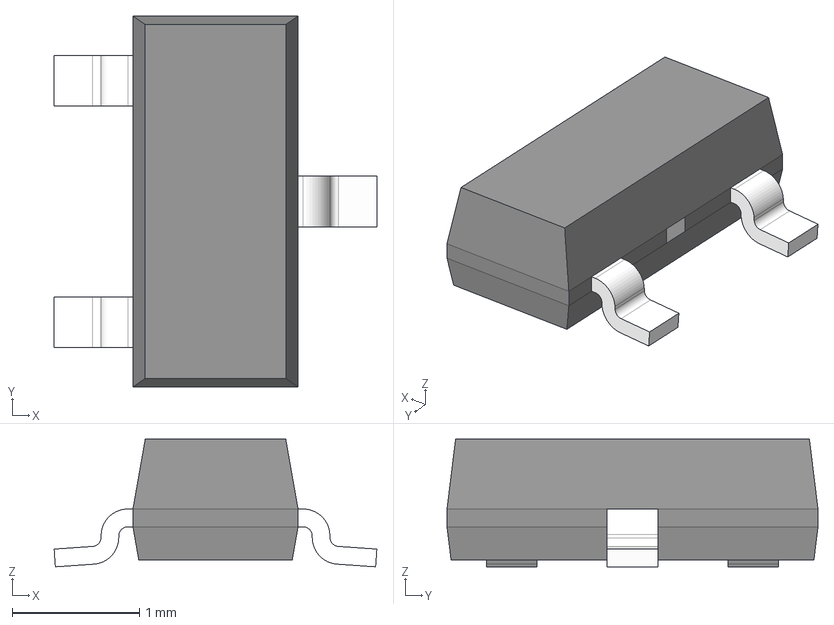
[picture p100: CAD file, 2023-09-02]
AxxSolder_hardware/3rd-parties-libraries/3D-models/TPD2E2U06QDBZRQ1.stp
2.54 x 2.92 x 1.01 mm
BODY-SOT
LEAD-SOT x 3
PIN1-ID
TIEBAR
