AxxAxx/AxxSolder/AxxSolder_hardware/3rd-parties-libraries/3D-models/PMEG10030ELPX.stp

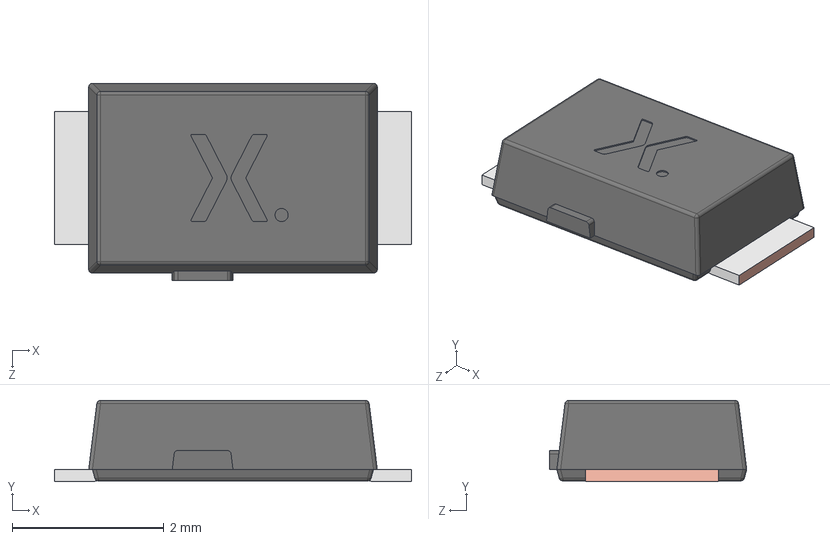
[picture p101: CAD file, 2023-09-02]
AxxSolder_hardware/3rd-parties-libraries/3D-models/PMEG10030ELPX.stp
4.70 x 1.07 x 2.60 mm
SOD128 Lead
SOD128 Lower body
SOD128 Upper body
