AxxAxx/AxxSolder/AxxSolder_hardware/3rd-parties-libraries/3D-models/STM32G431KBT6.stp

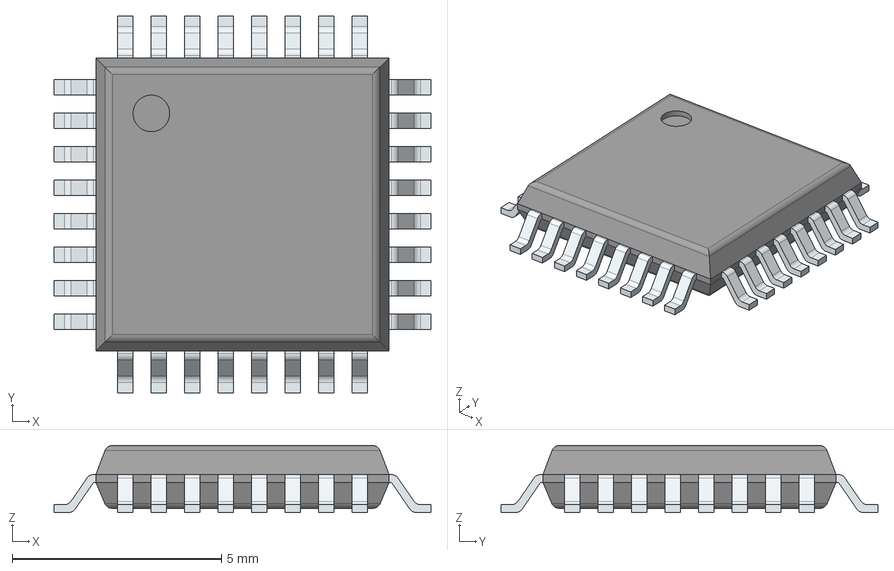
[picture p102: CAD file, 2023-09-02]
AxxSolder_hardware/3rd-parties-libraries/3D-models/STM32G431KBT6.stp
9.00 x 9.00 x 1.60 mm
PinsArrayLR
PinsArrayTB
