AxxAxx/AxxSolder/AxxSolder_hardware/3rd-parties-libraries/3D-models/LM358BAIDR.stp

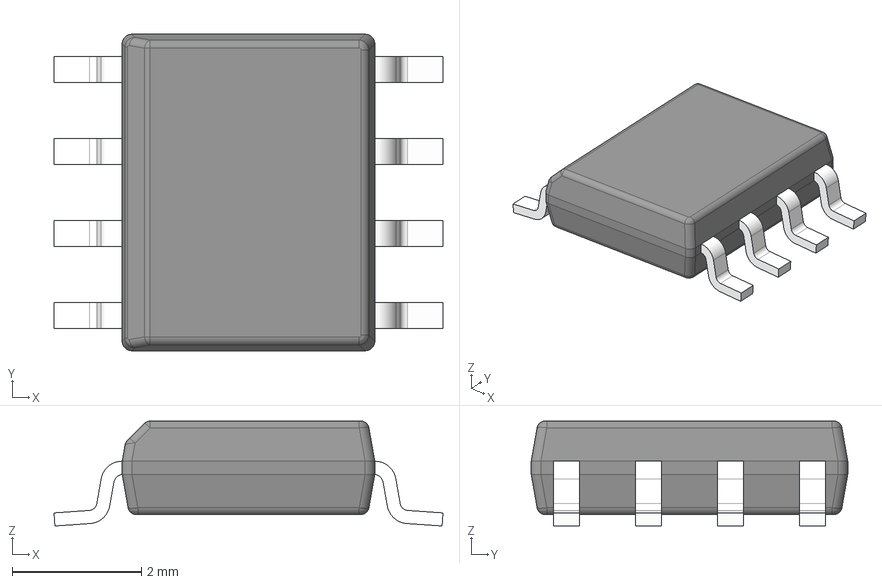
[picture p103: CAD file, 2023-09-02]
AxxSolder_hardware/3rd-parties-libraries/3D-models/LM358BAIDR.stp
6.02 x 4.90 x 1.63 mm
BODY-SO
LEAD-D0008A x 8
