AxxAxx/AxxSolder/AxxSolder_hardware/3rd-parties-libraries/3D-models/OPA2333AIDRBR.stp

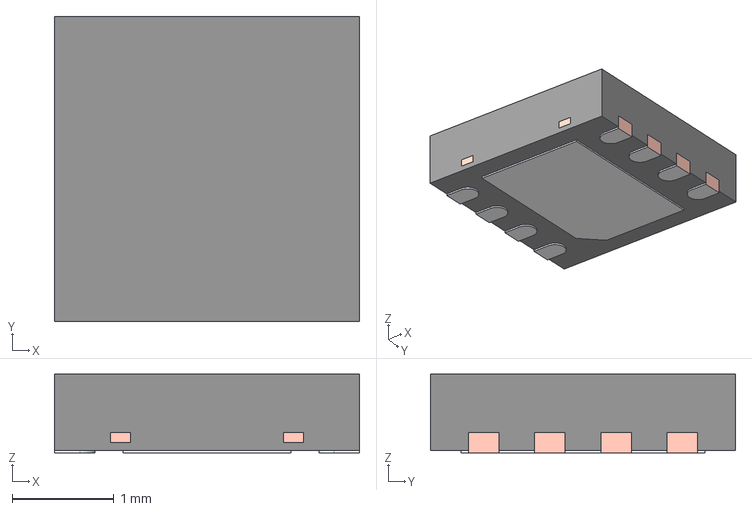
[picture p104: CAD file, 2023-09-02]
AxxSolder_hardware/3rd-parties-libraries/3D-models/OPA2333AIDRBR.stp
3.00 x 3.00 x 0.775 mm
BODY-SON
FRAME-DRB0008B
