AxxAxx/AxxSolder/AxxSolder_hardware/3rd-parties-libraries/3D-models/PMEG6020ER,115.stp

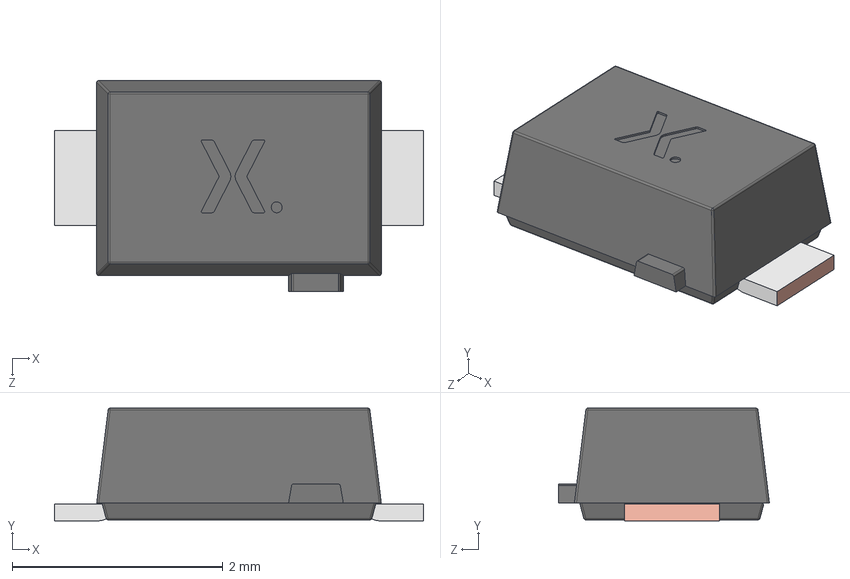
[picture p105: CAD file, 2023-09-02]
AxxSolder_hardware/3rd-parties-libraries/3D-models/PMEG6020ER,115.stp
3.50 x 1.07 x 2.00 mm
SOD123W Lower body
SOD123W Lead x 2
SOD123W Upper body
