AxxAxx/AxxSolder/CAD/Alternative_enclosures_and_designs/AxxSolder-LaborStation/AxxSolderFront.jpg

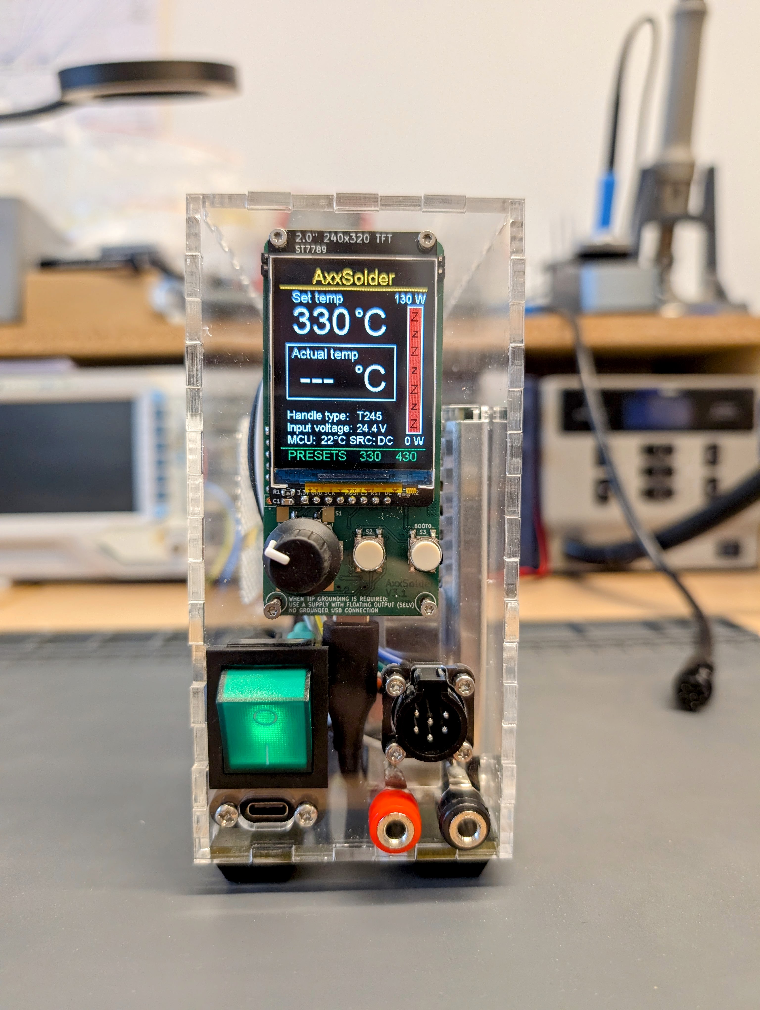
CAD/Alternative_enclosures_and_designs/AxxSolder-LaborStation/AxxSolderFront.jpg
