AxxAxx/AxxSolder/CAD/Alternative_enclosures_and_designs/AxxSolder-LaborStation/AxxSolderSide.jpg

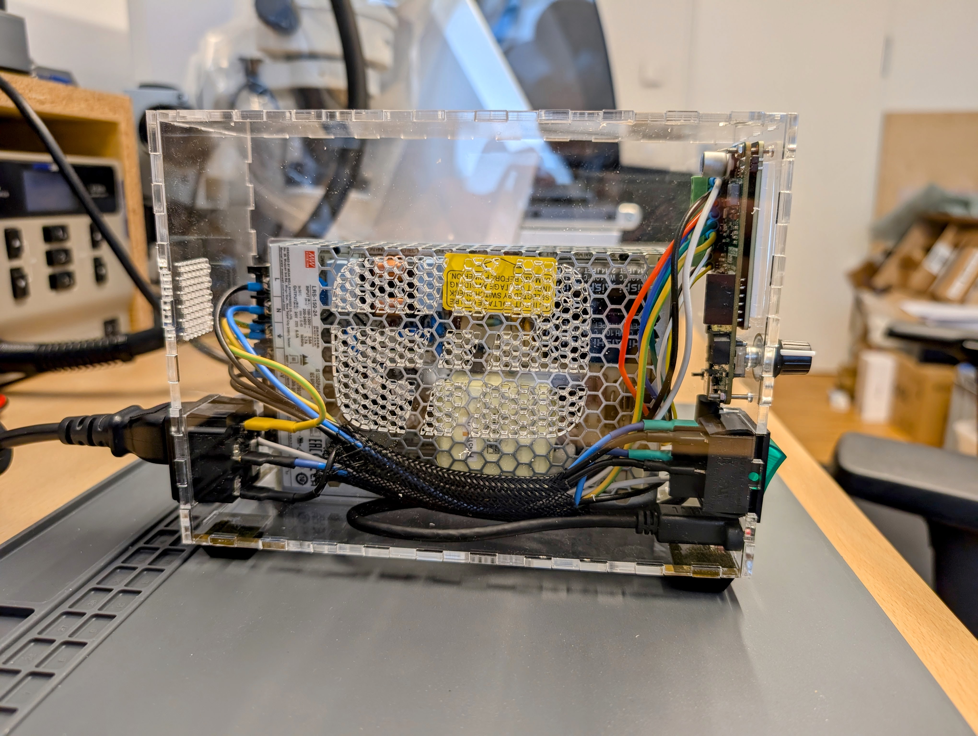
CAD/Alternative_enclosures_and_designs/AxxSolder-LaborStation/AxxSolderSide.jpg
