AxxAxx/AxxSolder/photos/AxxSolder_cover_Square.jpg

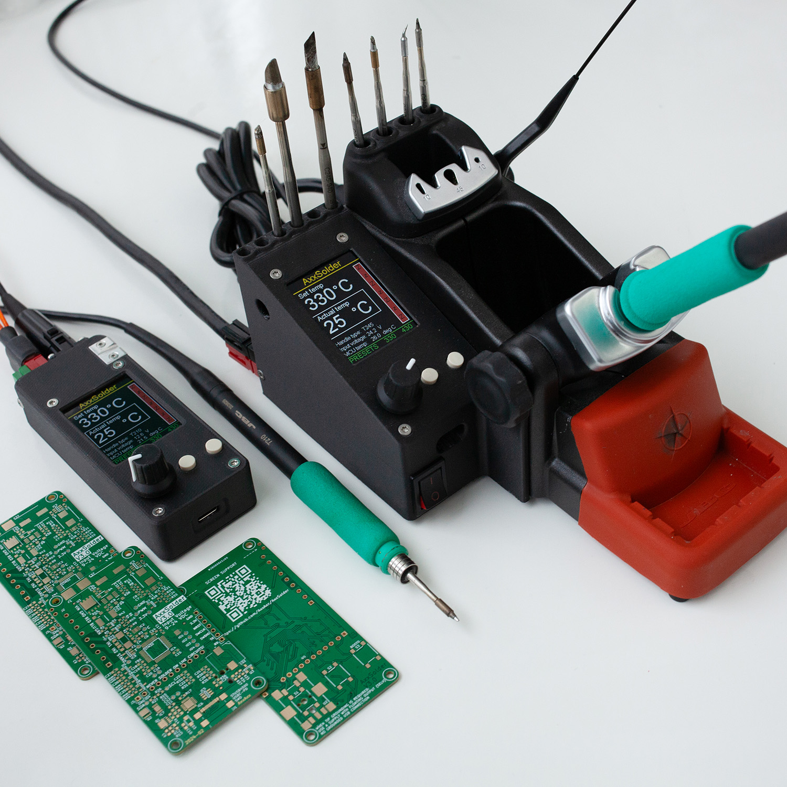
photos/AxxSolder_cover_Square.jpg
