AxxAxx/AxxSolder/photos/AxxSolder_PCBs.jpg

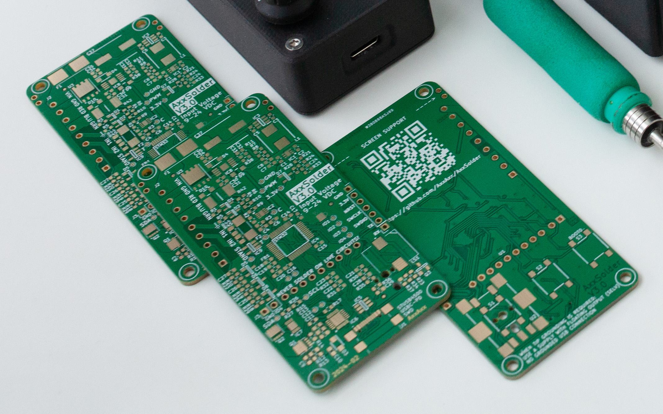
photos/AxxSolder_PCBs.jpg
