AxxAxx/AxxSolder/Other/Do not define DEBUG.png

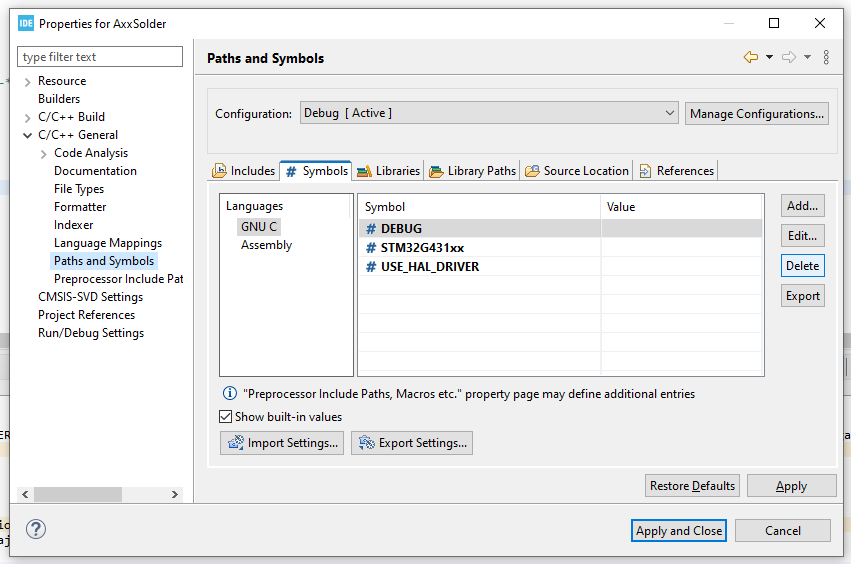
Other/Do not define DEBUG.png
