AxxAxx/AxxSolder/AxxSolder_firmware/Core/Inc/main.h

#define MAX_POWER 		150
#define MIN_SELECTABLE_TEMPERATURE 20
#define MAX_SELECTABLE_TEMPERATURE 450
#define PID_MAX_OUTPUT 500.0f
#define PID_UPDATE_INTERVAL 25
#define PID_ADD_I_MIN_ERROR 75
#define VERSION_BIT_1_Pin GPIO_PIN_13
#define VERSION_BIT_1_GPIO_Port GPIOC
#define VERSION_BIT_2_Pin GPIO_PIN_14
#define VERSION_BIT_2_GPIO_Port GPIOC
#define VERSION_BIT_3_Pin GPIO_PIN_15
#define VERSION_BIT_3_GPIO_Port GPIOC
#define HEATER_Pin GPIO_PIN_0
#define HEATER_GPIO_Port GPIOF
#define CURRENT_Pin GPIO_PIN_1
#define CURRENT_GPIO_Port GPIOF
#define ENC_A_Pin GPIO_PIN_0
#define ENC_A_GPIO_Port GPIOA
#define I_LEAK_Pin GPIO_PIN_1
#define I_LEAK_GPIO_Port GPIOA
#define VBUS_Pin GPIO_PIN_2
#define VBUS_GPIO_Port GPIOA
#define THERMOCOUPLE_Pin GPIO_PIN_3
#define THERMOCOUPLE_GPIO_Port GPIOA
#define HANDLE_INP_1_Pin GPIO_PIN_4
#define HANDLE_INP_1_GPIO_Port GPIOA
#define HANDLE_INP_2_Pin GPIO_PIN_5
#define HANDLE_INP_2_GPIO_Port GPIOA
#define STAND_INP_Pin GPIO_PIN_6
#define STAND_INP_GPIO_Port GPIOA
#define SW_2_Pin GPIO_PIN_7
#define SW_2_GPIO_Port GPIOA
#define SW_2_EXTI_IRQn EXTI9_5_IRQn
#define USR_2_Pin GPIO_PIN_0
#define USR_2_GPIO_Port GPIOB
#define USR_3_Pin GPIO_PIN_1
#define USR_3_GPIO_Port GPIOB
#define USR_4_Pin GPIO_PIN_2
#define USR_4_GPIO_Port GPIOB
#define SPI2_SD_CS_Pin GPIO_PIN_10
#define SPI2_SD_CS_GPIO_Port GPIOB
#define SPI2_DC_Pin GPIO_PIN_11
#define SPI2_DC_GPIO_Port GPIOB
#define SPI2_RST_Pin GPIO_PIN_12
#define SPI2_RST_GPIO_Port GPIOB
#define SPI2_CS_Pin GPIO_PIN_14
#define SPI2_CS_GPIO_Port GPIOB
#define USR_1_Pin GPIO_PIN_8
#define USR_1_GPIO_Port GPIOA
#define ENC_B_Pin GPIO_PIN_3
#define ENC_B_GPIO_Port GPIOB
#define SW_1_Pin GPIO_PIN_5
#define SW_1_GPIO_Port GPIOB
#define SW_1_EXTI_IRQn EXTI9_5_IRQn
#define BUZZER_Pin GPIO_PIN_7
#define BUZZER_GPIO_Port GPIOB
#define SW_3_Pin GPIO_PIN_8
#define SW_3_GPIO_Port GPIOB
#define SW_3_EXTI_IRQn EXTI9_5_IRQn
