AxxAxx/AxxSolder/AxxSolder_firmware/Core/Src/graph.c

#include "main.h"
#include "app_colors.h"   /* AxxSolder UI colour palette */
#include "lcd.h"
#include "display_app.h"   /* convert_temperature */
#include "settings.h"      /* flash_values */
#include "handle.h"        /* attached_handle (read by graph rendering) */
#include "util.h"          /* clamp */

#include "graph.h"

#include "string.h"
#include <stdio.h>
#include <math.h>

#include "gui.h"

// Functions responsible for displaying graphs on the display.
#define GRAPH_X0_vertical  38
#define GRAPH_Y0_vertical  270
#define GRAPH_WIDTH_vertical  160
#define GRAPH_HEIGHT_vertical 150

#define GRAPH_X0_horizontal  38
#define GRAPH_Y0_horizontal  215
#define GRAPH_WIDTH_horizontal  245
#define GRAPH_HEIGHT_horizontal 100

uint16_t GRAPH_X0;
uint16_t GRAPH_Y0;
uint16_t GRAPH_WIDTH;
uint16_t GRAPH_HEIGHT;

#define TEMP_MIN 0
#define TEMP_MAX_C 450
#define TEMP_MAX_F 850
#define POWER_MIN 0
#define POWER_MAX 100

#define GRAPH_POINTS 100


#define GRAPH_Color_TEMP        C_GraphTemp;          // Color of the temperature axis and graph in RUN mode
#define GRAPH_Color_SET_TEMP    C_GraphAxis;          // Color of the temperature axis and graph in RUN mode
#define GRAPH_Color_POWER       C_Header;     // Color of the power axis and graph in RUN mode

#define Color_TEMP_SLEEP        C_GraphPower         // Color of the temperature axis and graph in SLEEP mode
#define Color_POWER_SLEEP       C_GraphPowerSleep    // Color of the power axis and graph in SLEEP mode

#define Color_TIME              C_GraphAxis   // Color of the time axis

#define DASH_LEN_COLOR   C_GraphGrid   // Color of the dashed coordinate grid
#define DASH_LEN 5                     // Dash length in pixels
#define GAP_LEN  5                     // Gap length in pixels
#define THICKNESS_LEN  1               // Line thickness in pixels

uint16_t temp_array[GRAPH_POINTS];
uint16_t set_temp_array[GRAPH_POINTS];
uint16_t power_array[GRAPH_POINTS];
uint16_t prev_temp_array[GRAPH_POINTS];
uint16_t prev_set_temp_array[GRAPH_POINTS];
uint16_t prev_power_array[GRAPH_POINTS];
uint8_t index_graph = 0;

uint8_t initialized = 0;

// Structure for storing a line with its color
typedef struct {
    int x1, y1, x2, y2;
    uint16_t color;  // B_RED or B_BLUE or other
} Line;


void add_data_point(uint16_t temp, uint16_t power, uint16_t set_temp) {

	// Clamp value to keep the line within graph bounds
	if(flash_values.deg_celsius == 1){
		temp = clamp(temp, 0, TEMP_MAX_C);
		set_temp = clamp(set_temp, 0, TEMP_MAX_C);
	}
	else{
		temp = clamp(temp, 0, TEMP_MAX_F);
		set_temp = clamp(set_temp, 0, TEMP_MAX_F);
	}

	temp_array[index_graph] = temp;
    power_array[index_graph] = power;
    set_temp_array[index_graph] = set_temp;
    index_graph++;
    if (index_graph >= GRAPH_POINTS) index_graph = 0; // Circular buffer
}

static Line temp_lines_prev[GRAPH_POINTS - 1] = {0};
static Line set_temp_lines_prev[GRAPH_POINTS - 1] = {0};
static Line power_lines_prev[GRAPH_POINTS - 1] = {0};

// Universal dashed line using UG_FillFrame()
// dash_len  – dash length in pixels
// gap_len   – gap length in pixels
// thickness – line thickness in pixels
void draw_dashed_line_fillframe(int x1, int y1, int x2, int y2, uint16_t color,
                                uint8_t dash_len, uint8_t gap_len, uint8_t thickness) {
    int dx = abs(x2 - x1), sx = x1 < x2 ? 1 : -1;
    int dy = -abs(y2 - y1), sy = y1 < y2 ? 1 : -1;
    int err = dx + dy, e2;

    uint8_t phase = 0;          // Position within the dash or gap
    uint8_t draw = 1;           // Drawing or skipping
    uint8_t segment_len = dash_len;

    while (1) {
        if (draw) {
            UG_FillFrame(x1, y1, x1 + (thickness - 1), y1 + (thickness - 1), color);
        }
        phase++;
        if (phase >= segment_len) {
            phase = 0;
            draw = !draw; // Toggle draw mode
            segment_len = draw ? dash_len : gap_len;
        }

        if (x1 == x2 && y1 == y2) break;
        e2 = 2 * err;
        if (e2 >= dy) { err += dy; x1 += sx; }
        if (e2 <= dx) { err += dx; y1 += sy; }
    }
}

void draw_graph_init(void) {
	// Background, grid, and labels are drawn once
	UG_FillFrame(GRAPH_X0, GRAPH_Y0 - GRAPH_HEIGHT , GRAPH_X0 + GRAPH_WIDTH, GRAPH_Y0, background);

	if((flash_values.screen_rotation == 0) || (flash_values.screen_rotation == 2)){
		GRAPH_X0 = GRAPH_X0_vertical;
		GRAPH_Y0 = GRAPH_Y0_vertical;
		GRAPH_WIDTH = GRAPH_WIDTH_vertical;
		GRAPH_HEIGHT = GRAPH_HEIGHT_vertical;

		LCD_PutStr(53, 8, "AxxSolder", FONT_arial_19X22, C_Header, C_Background);
		LCD_DrawLine(0,36,240,36,C_Header);
		LCD_DrawLine(0,37,240,37,C_Header);
		LCD_DrawLine(0,38,240,38,C_Header);

		LCD_PutStr(10, 45, "Set temp:", FONT_arial_20X23, C_Text, C_Background);
		if(flash_values.deg_celsius == 1){
			LCD_PutStr(180, 45, "°C", FONT_arial_20X23, C_Text, C_Background);
		}
		else{
			LCD_PutStr(180, 45, "°F", FONT_arial_20X23, C_Text, C_Background);
		}
		LCD_PutStr(10, 70, "Actual temp:", FONT_arial_20X23, C_Text, C_Background);
		if(flash_values.deg_celsius == 1){
			LCD_PutStr(180, 70, "°C", FONT_arial_20X23, C_Text, C_Background);
		}
		else{
			LCD_PutStr(180, 70, "°F", FONT_arial_20X23, C_Text, C_Background);
		}

		LCD_PutStr(10, 95, "Handle:", FONT_arial_17X18, C_Text, C_Background);
		LCD_PutStr(127, 95, "Vin:", FONT_arial_17X18, C_Text, C_Background);

		UG_DrawLine(0, 296, 240, 296, C_Footer);
		UG_DrawLine(0, 297, 240, 297, C_Footer);

		if(flash_values.three_button_mode == 1){
			LCD_PutStr(11, 301, "TEMP          UP   DOWN", FONT_arial_20X23, C_Footer, C_Background);
		}
		else{
			char buf[16];
			LCD_PutStr(11, 301, "PRESETS", FONT_arial_20X23, C_Footer, C_Background);
			sprintf(buf, "%d", (int)convert_temperature(flash_values.preset_temp_1));
			LCD_PutStr(130, 301, buf, FONT_arial_20X23, C_Footer, C_Background);
			sprintf(buf, "%d", (int)convert_temperature(flash_values.preset_temp_2));
			LCD_PutStr(190, 301, buf, FONT_arial_20X23, C_Footer, C_Background);
		}

		// Time axis labels (X axis, in seconds)
	    float step_time_sec = ((float)GRAPH_WIDTH / 5.0f) * ((float)DISPLAY_TICK_INTERVAL_MS / 500.0f);

	    for (int i = 0; i <= 5; i++) {
	        int x_pos = GRAPH_X0 + i * (GRAPH_WIDTH / 5);
	        char buf[12];

	        if (i == 0) {
	            snprintf(buf, sizeof(buf), "0s");
	        } else {
	            // Format time without decimal places
	            snprintf(buf, sizeof(buf), "%d", (int)(i * step_time_sec));
	        }

	        int y_pos = GRAPH_Y0 + 4;

	        // Shift the last label left by 5 pixels
	        int x_draw = (i == 5) ? (x_pos - 5) : x_pos;

	        LCD_PutStr(x_draw, y_pos, buf, FONT_arial_17X18, Color_TIME, background);
	    }
	}
	else{
		GRAPH_X0 = GRAPH_X0_horizontal;
		GRAPH_Y0 = GRAPH_Y0_horizontal;
		GRAPH_WIDTH = GRAPH_WIDTH_horizontal;
		GRAPH_HEIGHT = GRAPH_HEIGHT_horizontal;

		LCD_PutStr(90, 8, "AxxSolder", FONT_arial_19X22, C_Header, C_Background);
		LCD_DrawLine(0,36,310,36,C_Header);
		LCD_DrawLine(0,37,310,37,C_Header);
		LCD_DrawLine(0,38,310,38,C_Header);

		LCD_PutStr(10, 45, "Set temp:", FONT_arial_20X23, C_Text, C_Background);
		if(flash_values.deg_celsius == 1){
			LCD_PutStr(180, 45, "°C", FONT_arial_20X23, C_Text, C_Background);
		}
		else{
			LCD_PutStr(180, 45, "°F", FONT_arial_20X23, C_Text, C_Background);
		}
		LCD_PutStr(10, 70, "Actual temp:", FONT_arial_20X23, C_Text, C_Background);
		if(flash_values.deg_celsius == 1){
			LCD_PutStr(180, 70, "°C", FONT_arial_20X23, C_Text, C_Background);
		}
		else{
			LCD_PutStr(180, 70, "°F", FONT_arial_20X23, C_Text, C_Background);
		}

		LCD_PutStr(10, 95, "Handle:", FONT_arial_17X18, C_Text, C_Background);
		LCD_PutStr(126, 95, "Vin:", FONT_arial_17X18, C_Text, C_Background);

		//LCD_PutStr(205, 95, "AxxSolder", FONT_arial_17X18, C_Header, C_Background);

		// Time axis labels (X axis, in seconds)
	    float step_time_sec = ((float)GRAPH_WIDTH / 5.0f) * ((float)DISPLAY_TICK_INTERVAL_MS / 750.0f);

	    for (int i = 0; i <= 5; i++) {
	        int x_pos = GRAPH_X0 + i * (GRAPH_WIDTH / 5);
	        char buf[12];

	        if (i == 0) {
	            snprintf(buf, sizeof(buf), "0s");
	        } else {
	            // Format time without decimal places
	            snprintf(buf, sizeof(buf), "%d", (int)(i * step_time_sec));
	        }

	        int y_pos = GRAPH_Y0 + 4;

	        // Shift the last label left by 5 pixels
	        int x_draw = (i == 5) ? (x_pos - 5) : x_pos;

	        LCD_PutStr(x_draw, y_pos, buf, FONT_arial_17X18, Color_TIME, background);
	    }
	}

    // Draw horizontal dashed lines
    for (int y = 0; y <= GRAPH_HEIGHT; y += GRAPH_HEIGHT / 5) {
        draw_dashed_line_fillframe(GRAPH_X0, GRAPH_Y0 - y, GRAPH_X0 + GRAPH_WIDTH, GRAPH_Y0 - y,
        		DASH_LEN_COLOR, DASH_LEN, GAP_LEN, THICKNESS_LEN); // dash=1, gap=5, thickness=1
    }

    // Draw vertical dashed lines
    for (int x = 0; x <= GRAPH_WIDTH; x += GRAPH_WIDTH / 5) {
        draw_dashed_line_fillframe(GRAPH_X0 + x, GRAPH_Y0 - GRAPH_HEIGHT, GRAPH_X0 + x, GRAPH_Y0,
        		DASH_LEN_COLOR, DASH_LEN, GAP_LEN, THICKNESS_LEN);
    }



    initialized = 1;
}

// Universal function for a line with a specified thickness
void draw_line_with_thickness(int x1, int y1, int x2, int y2, uint16_t color, uint8_t thickness) {
    int dx = abs(x2 - x1), sx = x1 < x2 ? 1 : -1;
    int dy = -abs(y2 - y1), sy = y1 < y2 ? 1 : -1;
    int err = dx + dy, e2;

    while (1) {
        // Thickness in pixels (square brush)
        UG_FillFrame(x1, y1, x1 + (thickness - 1), y1 + (thickness - 1), color);

        if (x1 == x2 && y1 == y2) break;
        e2 = 2 * err;
        if (e2 >= dy) { err += dy; x1 += sx; }
        if (e2 <= dx) { err += dx; y1 += sy; }
    }
}

// Restore the dashed grid at a given point
void restore_grid_point(int x, int y) {
    // Horizontal grid lines
    for (int gy = 0; gy <= GRAPH_HEIGHT; gy += GRAPH_HEIGHT / 5) {
        int grid_y = GRAPH_Y0 - gy;
        if (abs(y - grid_y) <= THICKNESS_LEN) {
            int cycle_len = DASH_LEN + GAP_LEN;
            int dash_index = (x - GRAPH_X0) / cycle_len;
            int dash_start = GRAPH_X0 + dash_index * cycle_len;
            int dash_end = dash_start + DASH_LEN - 1;

            if (dash_end > GRAPH_X0 + GRAPH_WIDTH) dash_end = GRAPH_X0 + GRAPH_WIDTH;

            // Draw the full dash segment
            UG_FillFrame(dash_start, grid_y,
                         dash_end,   grid_y,
						 DASH_LEN_COLOR);
            return;
        }
    }

    // Vertical grid lines
    for (int gx = 0; gx <= GRAPH_WIDTH; gx += GRAPH_WIDTH / 5) {
        int grid_x = GRAPH_X0 + gx;
        if (abs(x - grid_x) <= THICKNESS_LEN) {
            int cycle_len = DASH_LEN + GAP_LEN;
            int dash_index = (GRAPH_Y0 - y) / cycle_len;
            int dash_start = GRAPH_Y0 - dash_index * cycle_len;
            int dash_end = dash_start - (DASH_LEN - 1);

            if (dash_end < GRAPH_Y0 - GRAPH_HEIGHT) dash_end = GRAPH_Y0 - GRAPH_HEIGHT;

            UG_FillFrame(grid_x,
                         dash_end, grid_x,
                         dash_start,
						 DASH_LEN_COLOR);
            return;
        }
    }
}

// Erases a line with 2-pixel thickness and restores the grid
void erase_line_and_restore_grid(int x1, int y1, int x2, int y2) {
    // Erase with 2-pixel thickness
    draw_line_with_thickness(x1, y1, x2, y2, background, 2);

    int dx = abs(x2 - x1);
    int dy = abs(y2 - y1);

    int sx = (x1 < x2) ? 1 : -1;
    int sy = (y1 < y2) ? 1 : -1;

    int err = dx - dy;

    while (1) {
        restore_grid_point(x1, y1);

        if (x1 == x2 && y1 == y2)
            break;

        int e2 = err * 2;
        if (e2 > -dy) {
            err -= dy;
            x1 += sx;
        }
        if (e2 < dx) {
            err += dx;
            y1 += sy;
        }
    }
}


// Check whether two line segments overlap within their bounding rectangles, with a thickness margin
bool lines_overlap(Line *l1, Line *l2, int thickness) {
    int l1_xmin = l1->x1 < l1->x2 ? l1->x1 : l1->x2;
    int l1_xmax = l1->x1 > l1->x2 ? l1->x1 : l1->x2;
    int l1_ymin = l1->y1 < l1->y2 ? l1->y1 : l1->y2;
    int l1_ymax = l1->y1 > l1->y2 ? l1->y1 : l1->y2;

    int l2_xmin = l2->x1 < l2->x2 ? l2->x1 : l2->x2;
    int l2_xmax = l2->x1 > l2->x2 ? l2->x1 : l2->x2;
    int l2_ymin = l2->y1 < l2->y2 ? l2->y1 : l2->y2;
    int l2_ymax = l2->y1 > l2->y2 ? l2->y1 : l2->y2;

    // Add thickness margin for overlap detection
    l1_xmin -= thickness;
    l1_xmax += thickness;
    l1_ymin -= thickness;
    l1_ymax += thickness;

    l2_xmin -= thickness;
    l2_xmax += thickness;
    l2_ymin -= thickness;
    l2_ymax += thickness;

    bool x_overlap = (l1_xmin <= l2_xmax) && (l1_xmax >= l2_xmin);
    bool y_overlap = (l1_ymin <= l2_ymax) && (l1_ymax >= l2_ymin);

    return x_overlap && y_overlap;
}

// Helper function for drawing an axis with labels
// values       - array of values for the labels
// count        - number of labels in the array
// x            - horizontal position for rendering labels
// is_left_axis - true if the axis is on the left (labels on the left), false for right
// unit_start   - suffix for the first label (e.g. "°C" or "%"), may be NULL
// unit_end     - suffix for the last label, may be NULL
void draw_axis(const int *values, int count, int x, bool is_left_axis,
               uint16_t color, const char *unit_start, const char *unit_end) {
    // Top and bottom Y boundaries so labels don't exceed the grid
    int y_min = GRAPH_Y0 - GRAPH_HEIGHT + 15; // Slightly below the top grid line
    //int y_max = GRAPH_Y0 - 1;                 // Slightly above the bottom grid line
    int y_max = GRAPH_Y0+5;                    // Visually on the bottom grid line

    for (int i = 0; i < count; i++) {
        int y_pos;

        if (i == 0) {
            y_pos = y_max;  // Bottom label (minimum value)
        } else if (i == count - 1) {
            y_pos = y_min;  // Top label (maximum value)
        } else {
            // Evenly distribute remaining labels between top and bottom boundaries
            float fraction = (float)i / (count - 1);
            y_pos = y_max - (int)((y_max - y_min) * fraction);
        }

        char buf[12];

        // Add unit suffix only for the first label, others without units
        if (i == 0 && unit_start) {
            snprintf(buf, sizeof(buf), "%d%s", values[i], unit_start);
        } else {
            snprintf(buf, sizeof(buf), "%d", values[i]);
        }

        // For the left axis use a fixed left offset (2 pixels)
        int x_pos = x;
        if (is_left_axis) {
            x_pos = 6;
        }

        // Render label with a -15 vertical offset for visual alignment
        LCD_PutStr(x_pos, y_pos - 15, buf, FONT_arial_17X18, color, background);
    }
}

// Update axis label colors depending on sensor_values.current_state
void draw_axis_labels(void) {
    // Choose label colors once based on current state
    //uint16_t color_temp_label = (sensor_values.current_state == RUN) ? GRAPH_Color_TEMP : Color_TEMP_SLEEP;
    //uint16_t color_power_label = (sensor_values.current_state == RUN) ? GRAPH_Color_POWER : Color_POWER_SLEEP;
    uint16_t color_temp_label = GRAPH_Color_TEMP;
    uint16_t color_power_label = GRAPH_Color_POWER;

    // Value arrays for the temperature and power axes
    int temp_values_C[] = {0, 90, 180, 270, 360, 450};
    int temp_values_F[] = {0, 170, 340, 510, 680, 850};
    int power_values[] = {0, 20, 40, 60, 80, 100};

    // Draw the left temperature axis (with °C symbol on the minimum value)
    if(flash_values.deg_celsius == 1){
    	draw_axis(temp_values_C, sizeof(temp_values_C)/sizeof(temp_values_C[0]), 2, true, color_temp_label, "°C", NULL);
    }
    else{
    	draw_axis(temp_values_F, sizeof(temp_values_F)/sizeof(temp_values_F[0]), 2, true, color_temp_label, "°F", NULL);
    }

    // Draw the right power axis (with % on the minimum value)
    draw_axis(power_values, sizeof(power_values)/sizeof(power_values[0]), GRAPH_X0 + GRAPH_WIDTH + 3, false, color_power_label, "%", "");
}


void check_and_update_labels(void) {
	uint8_t last_sensor_state = 0xFF;
	if (last_sensor_state != sensor_values.current_state) {
        draw_axis_labels();
        last_sensor_state = sensor_values.current_state;
    }
}

void draw_graph_update(void) {
    if (!initialized) {
        draw_graph_init();
    }

    check_and_update_labels();

    //uint16_t color_temp = (sensor_values.current_state == RUN) ? GRAPH_Color_TEMP : Color_TEMP_SLEEP;
    //uint16_t color_power = (sensor_values.current_state == RUN) ? GRAPH_Color_POWER : Color_POWER_SLEEP;
    uint16_t color_temp = GRAPH_Color_TEMP;
    uint16_t color_set_temp = GRAPH_Color_SET_TEMP;
    uint16_t color_power = GRAPH_Color_POWER;

    // Update temperature and power lines with partial erasing
    for (uint8_t i = 1; i < GRAPH_POINTS; i++) {

        // Most recently added data will be on the right (graph moves left to right)
        uint8_t idx_prev = (index_graph + GRAPH_POINTS - i) % GRAPH_POINTS;
        uint8_t idx_curr = (index_graph + GRAPH_POINTS - i - 1) % GRAPH_POINTS;

        int x_prev_temp = GRAPH_X0 + ((i - 1) * GRAPH_WIDTH) / (GRAPH_POINTS - 1);
        int x_curr_temp = GRAPH_X0 + (i * GRAPH_WIDTH) / (GRAPH_POINTS - 1);

        int x_prev_set_temp = GRAPH_X0 + ((i - 1) * GRAPH_WIDTH) / (GRAPH_POINTS - 1);
        int x_curr_set_temp = GRAPH_X0 + (i * GRAPH_WIDTH) / (GRAPH_POINTS - 1);

        // Temp lines
        int y_prev_temp = 0;
        int y_curr_temp = 0;
    	if(flash_values.deg_celsius == 1){
    		y_prev_temp = GRAPH_Y0 - ((temp_array[idx_prev] - TEMP_MIN) * GRAPH_HEIGHT) / (TEMP_MAX_C - TEMP_MIN);
    		y_curr_temp = GRAPH_Y0 - ((temp_array[idx_curr] - TEMP_MIN) * GRAPH_HEIGHT) / (TEMP_MAX_C - TEMP_MIN);
    	}
    	else{
    		y_prev_temp = GRAPH_Y0 - ((temp_array[idx_prev] - TEMP_MIN) * GRAPH_HEIGHT) / (TEMP_MAX_F - TEMP_MIN);
    		y_curr_temp = GRAPH_Y0 - ((temp_array[idx_curr] - TEMP_MIN) * GRAPH_HEIGHT) / (TEMP_MAX_F - TEMP_MIN);
    	}

        Line new_temp_line = {x_prev_temp, y_prev_temp, x_curr_temp, y_curr_temp, color_temp};
        Line *old_temp_line = &temp_lines_prev[i - 1];

        // Set_Temp lines
        int y_prev_set_temp = 0;
        int y_curr_set_temp = 0;
    	if(flash_values.deg_celsius == 1){
    		y_prev_set_temp = GRAPH_Y0 - ((set_temp_array[idx_prev] - TEMP_MIN) * GRAPH_HEIGHT) / (TEMP_MAX_C - TEMP_MIN);
    		y_curr_set_temp = GRAPH_Y0 - ((set_temp_array[idx_curr] - TEMP_MIN) * GRAPH_HEIGHT) / (TEMP_MAX_C - TEMP_MIN);
    	}
    	else{
    		y_prev_set_temp = GRAPH_Y0 - ((set_temp_array[idx_prev] - TEMP_MIN) * GRAPH_HEIGHT) / (TEMP_MAX_F - TEMP_MIN);
    		y_curr_set_temp = GRAPH_Y0 - ((set_temp_array[idx_curr] - TEMP_MIN) * GRAPH_HEIGHT) / (TEMP_MAX_F - TEMP_MIN);
    	}

        Line new_set_temp_line = {x_prev_set_temp, y_prev_set_temp, x_curr_set_temp, y_curr_set_temp, color_set_temp};
        Line *old_set_temp_line = &set_temp_lines_prev[i - 1];


        // Power lines
        int x_prev_power = x_prev_temp;
        int x_curr_power = x_curr_temp;
        int y_prev_power = (GRAPH_Y0 - ((power_array[idx_prev] - POWER_MIN) * GRAPH_HEIGHT) / (POWER_MAX - POWER_MIN));
        int y_curr_power = (GRAPH_Y0 - ((power_array[idx_curr] - POWER_MIN) * GRAPH_HEIGHT) / (POWER_MAX - POWER_MIN));


        Line new_power_line = {x_prev_power, y_prev_power, x_curr_power, y_curr_power, color_power};
        Line *old_power_line = &power_lines_prev[i - 1];

        bool temp_line_changed = (old_temp_line->x1 != new_temp_line.x1) || (old_temp_line->y1 != new_temp_line.y1) ||
                                 (old_temp_line->x2 != new_temp_line.x2) || (old_temp_line->y2 != new_temp_line.y2) ||
                                 (old_temp_line->color != new_temp_line.color);

        bool set_temp_line_changed = (old_set_temp_line->x1 != new_set_temp_line.x1) || (old_set_temp_line->y1 != new_set_temp_line.y1) ||
                                 (old_set_temp_line->x2 != new_set_temp_line.x2) || (old_set_temp_line->y2 != new_set_temp_line.y2) ||
                                 (old_set_temp_line->color != new_set_temp_line.color);

        bool power_line_changed = (old_power_line->x1 != new_power_line.x1) || (old_power_line->y1 != new_power_line.y1) ||
                                  (old_power_line->x2 != new_power_line.x2) || (old_power_line->y2 != new_power_line.y2) ||
                                  (old_power_line->color != new_power_line.color);

        // Check for overlap between old lines if at least one line has changed
        if (temp_line_changed || set_temp_line_changed || power_line_changed) {
            bool overlap = false;

            if ((old_temp_line->x1 || old_temp_line->y1 || old_temp_line->x2 || old_temp_line->y2) &&
            	(old_set_temp_line->x1 || old_set_temp_line->y1 || old_set_temp_line->x2 || old_set_temp_line->y2) &&
                (old_power_line->x1 || old_power_line->y1 || old_power_line->x2 || old_power_line->y2)) {
                overlap = lines_overlap(old_temp_line, old_power_line, 2);
            }

            if (overlap) {
                // Erase both lines and restore the grid
                erase_line_and_restore_grid(old_temp_line->x1, old_temp_line->y1, old_temp_line->x2, old_temp_line->y2);
                erase_line_and_restore_grid(old_set_temp_line->x1, old_set_temp_line->y1, old_set_temp_line->x2, old_set_temp_line->y2);
                erase_line_and_restore_grid(old_power_line->x1, old_power_line->y1, old_power_line->x2, old_power_line->y2);
            } else {
                // Erase only the changed lines individually
                if (temp_line_changed && (old_temp_line->x1 || old_temp_line->y1 || old_temp_line->x2 || old_temp_line->y2)) {
                    erase_line_and_restore_grid(old_temp_line->x1, old_temp_line->y1, old_temp_line->x2, old_temp_line->y2);
                }
                if (set_temp_line_changed && (old_set_temp_line->x1 || old_set_temp_line->y1 || old_set_temp_line->x2 || old_set_temp_line->y2)) {
                    erase_line_and_restore_grid(old_set_temp_line->x1, old_set_temp_line->y1, old_set_temp_line->x2, old_set_temp_line->y2);
                }
                if (power_line_changed && (old_power_line->x1 || old_power_line->y1 || old_power_line->x2 || old_power_line->y2)) {
                    erase_line_and_restore_grid(old_power_line->x1, old_power_line->y1, old_power_line->x2, old_power_line->y2);
                }
            }
        }

        // Draw new lines
        draw_line_with_thickness(new_set_temp_line.x1, new_set_temp_line.y1, new_set_temp_line.x2, new_set_temp_line.y2, new_set_temp_line.color, 2);
        draw_line_with_thickness(new_temp_line.x1, new_temp_line.y1, new_temp_line.x2, new_temp_line.y2, new_temp_line.color, 2);
        draw_line_with_thickness(new_power_line.x1, new_power_line.y1, new_power_line.x2, new_power_line.y2, new_power_line.color, 2);

        // Save new lines to prev
        temp_lines_prev[i - 1] = new_temp_line;
        set_temp_lines_prev[i - 1] = new_set_temp_line;
        power_lines_prev[i - 1] = new_power_line;
    }
}
