AxxAxx/AxxSolder/AxxSolder_firmware/Drivers/LCD/images.c

#include "images.h"


// For the picture: https://sourceforge.net/projects/lcd-image-converter
// Image settings: Preset Color R5G6B5, Block size 16, Little-Endian, rest is left with default
const uint16_t fry_data [8778] = {
    0x4b10, 0x4b10, 0x4b10, 0x4b10, 0x4b10, 0x4b10, 0x4b10, 0x4b10, 0x4b10, 0x4b10, 0x4b10, 0x4b10, 0x4b10, 0x4b10, 0x4b10, 0x4b10, 0x4b10, 0x4b10, 0x4b10, 0xa618, 0xc6f8, 0x4b10, 0x4b10, 0xc6f8, 0xa514, 0x4b10, 0x4b10, 0xc618, 0xffff, 0xffde, 0x8510, 0x4b10, 0x4b10, 0x4b10, 0x4b10, 0xa618, 0xc6f8, 0xc6f8, 0xc6f8, 0x4b10, 0xa514, 0xc6f8, 0xc6f8, 0xc618, 0xa514, 0x4b10, 0x4b10, 0xa514, 0xc6f8, 0xc6f8, 0xc6f8, 0xa514, 0x4b10, 0x4b10, 0x4b10, 0xc618, 0xffff, 0xffde, 0x8410, 0x4b10, 0x4b10, 0xc6f8, 0xc6f8, 0xc6f8, 0xc618, 0x6310, 0x4b10, 0x4b10, 0x8510, 0xffde, 0xffff, 0xc618, 0x4208, 0x4b10, 0x4b10, 0x4b10, 0x4b10,
    0x4b10, 0x4b10, 0x4b10, 0x4b10, 0x4b10, 0x4b10, 0x4b10, 0x4b10, 0x4b10, 0x4b10, 0x4b10, 0x4b10, 0x4b10, 0x4b10, 0x4b10, 0x4b10, 0x4b10, 0x4b10, 0x4b10, 0xc6f8, 0xffff, 0x8410, 0x4b10, 0xffff, 0xc6f8, 0x4b10, 0xa618, 0xffff, 0xffde, 0xffde, 0xffff, 0x6310, 0x4b10, 0x4b10, 0x4b10, 0xffde, 0xffff, 0xffff, 0xffff, 0x4b10, 0xa514, 0xffff, 0xffff, 0xffde, 0xffff, 0xa618, 0x4b10, 0xc618, 0xffff, 0xffff, 0xffde, 0xffff, 0x8410, 0x4b10, 0xc618, 0xffff, 0xffde, 0xffde, 0xffff, 0x6308, 0x4b10, 0xffff, 0xffff, 0xffde, 0xffff, 0xffde, 0x4b10, 0x4208, 0xffde, 0xffff, 0xffde, 0xffff, 0xc618, 0x4b10, 0x4b10, 0x4b10, 0x4b10,
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
};


UG_BMP fry = {
  .p=fry_data,
  .width=77,
  .height=114,
  .bpp=BMP_BPP_16,
};
