AxxAxx/AxxSolder/AxxSolder_firmware/Core/Inc/menu_profiles.h

#ifndef MENU_PROFILES_H
#define MENU_PROFILES_H

#include "main.h"
#include "handle.h"   /* enum handles */

/* Full profiles editor — called from settings_menu when "Profiles" group selected */
void profiles_menu(void);

void profiles_menu(void);

void profiles_reset(void);
void profiles_save(void);

/* Quick profile selector popup — called on handle change if enabled */
void profiles_popup(enum handles h);

#endif /* MENU_PROFILES_H */
